Ingwie/OpenAVRc_Dev/documentation/Schema_MegaMini.pdf

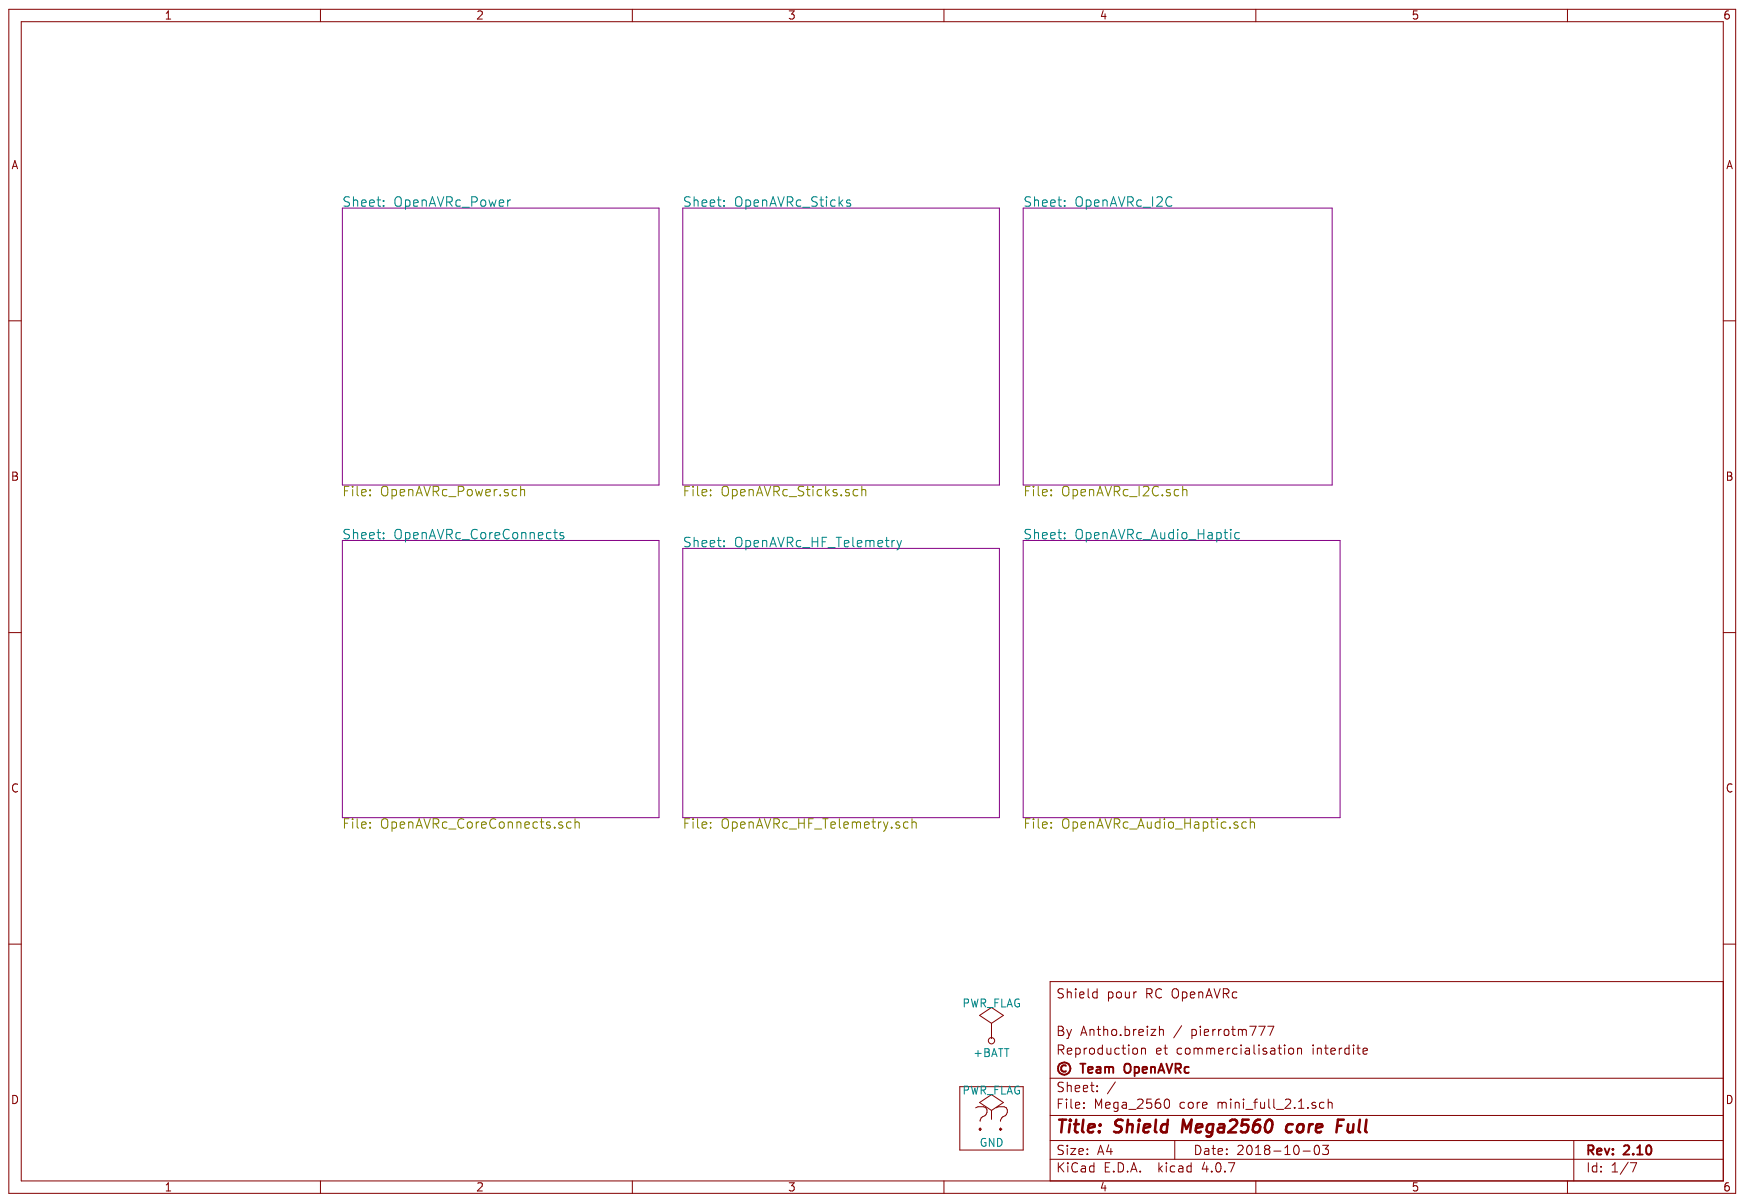
[picture p331: page 1]

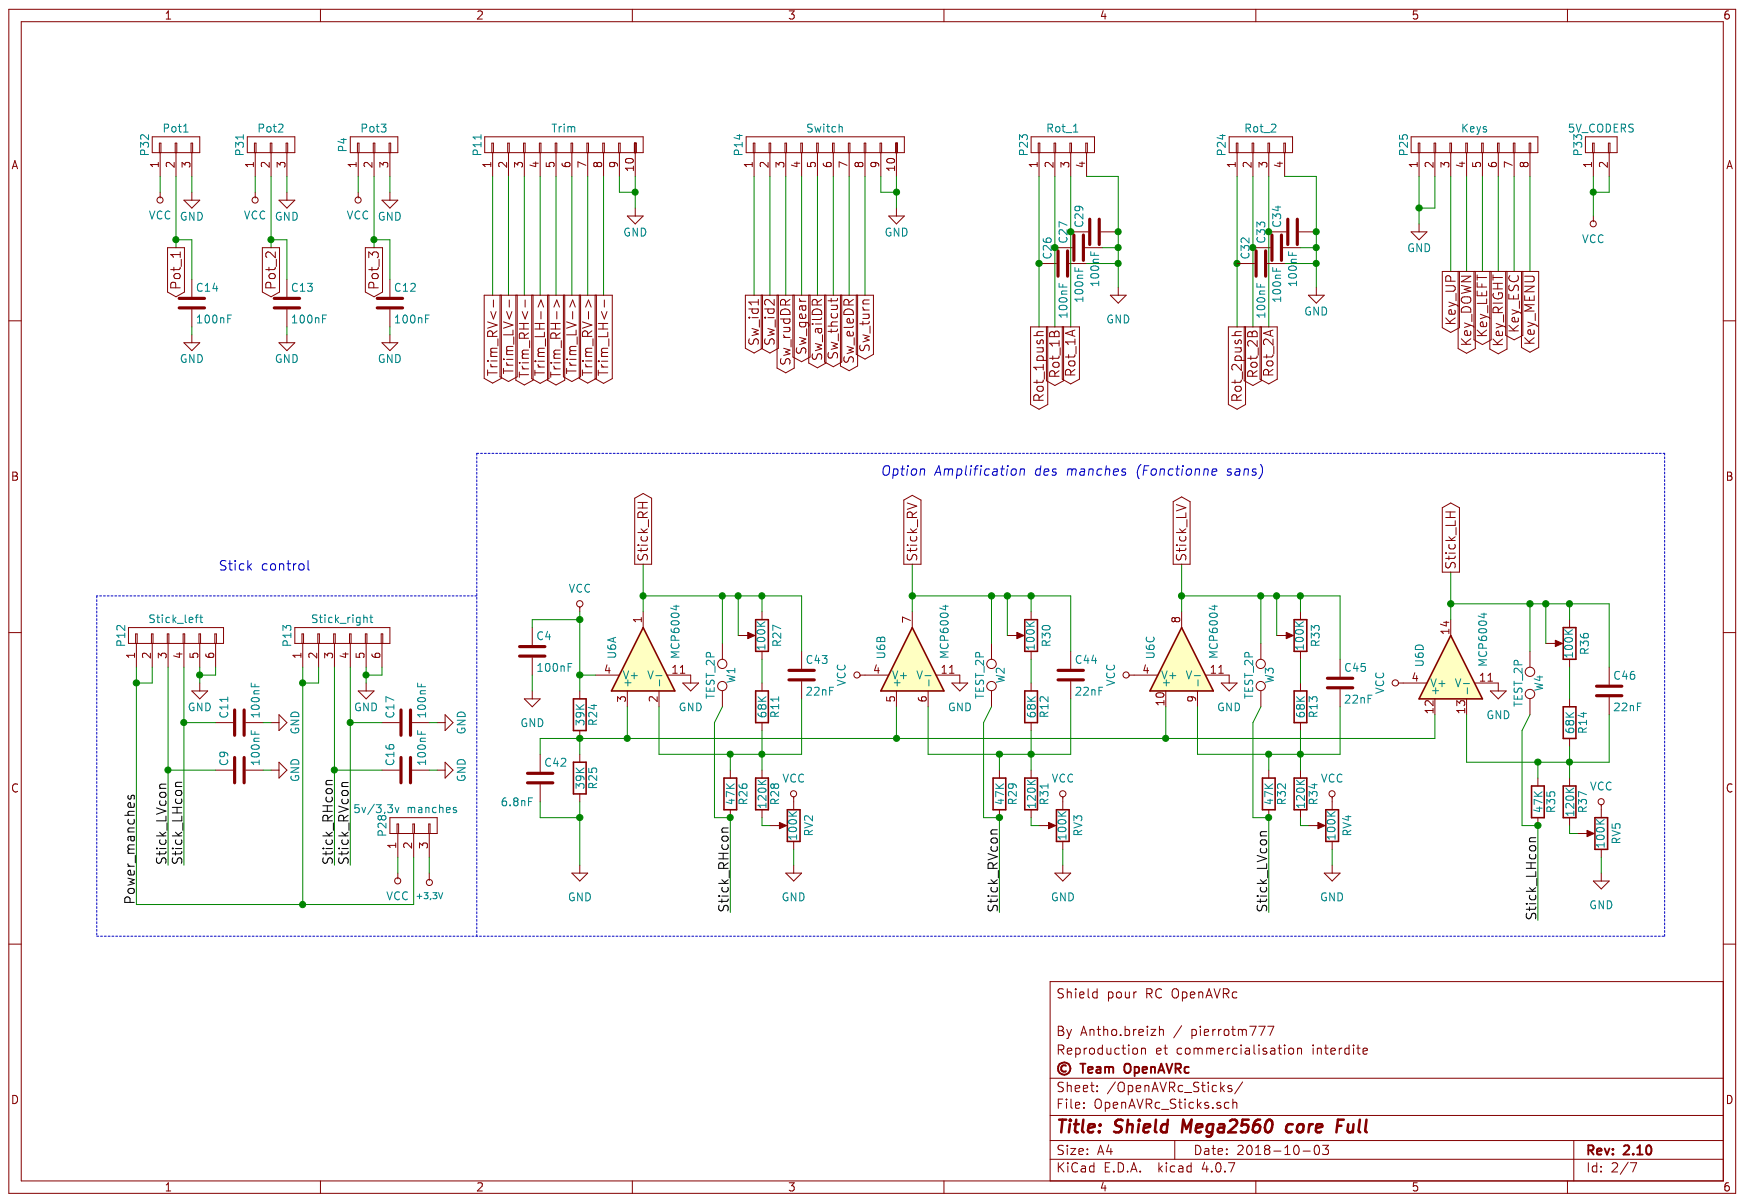
[picture p332: page 2]

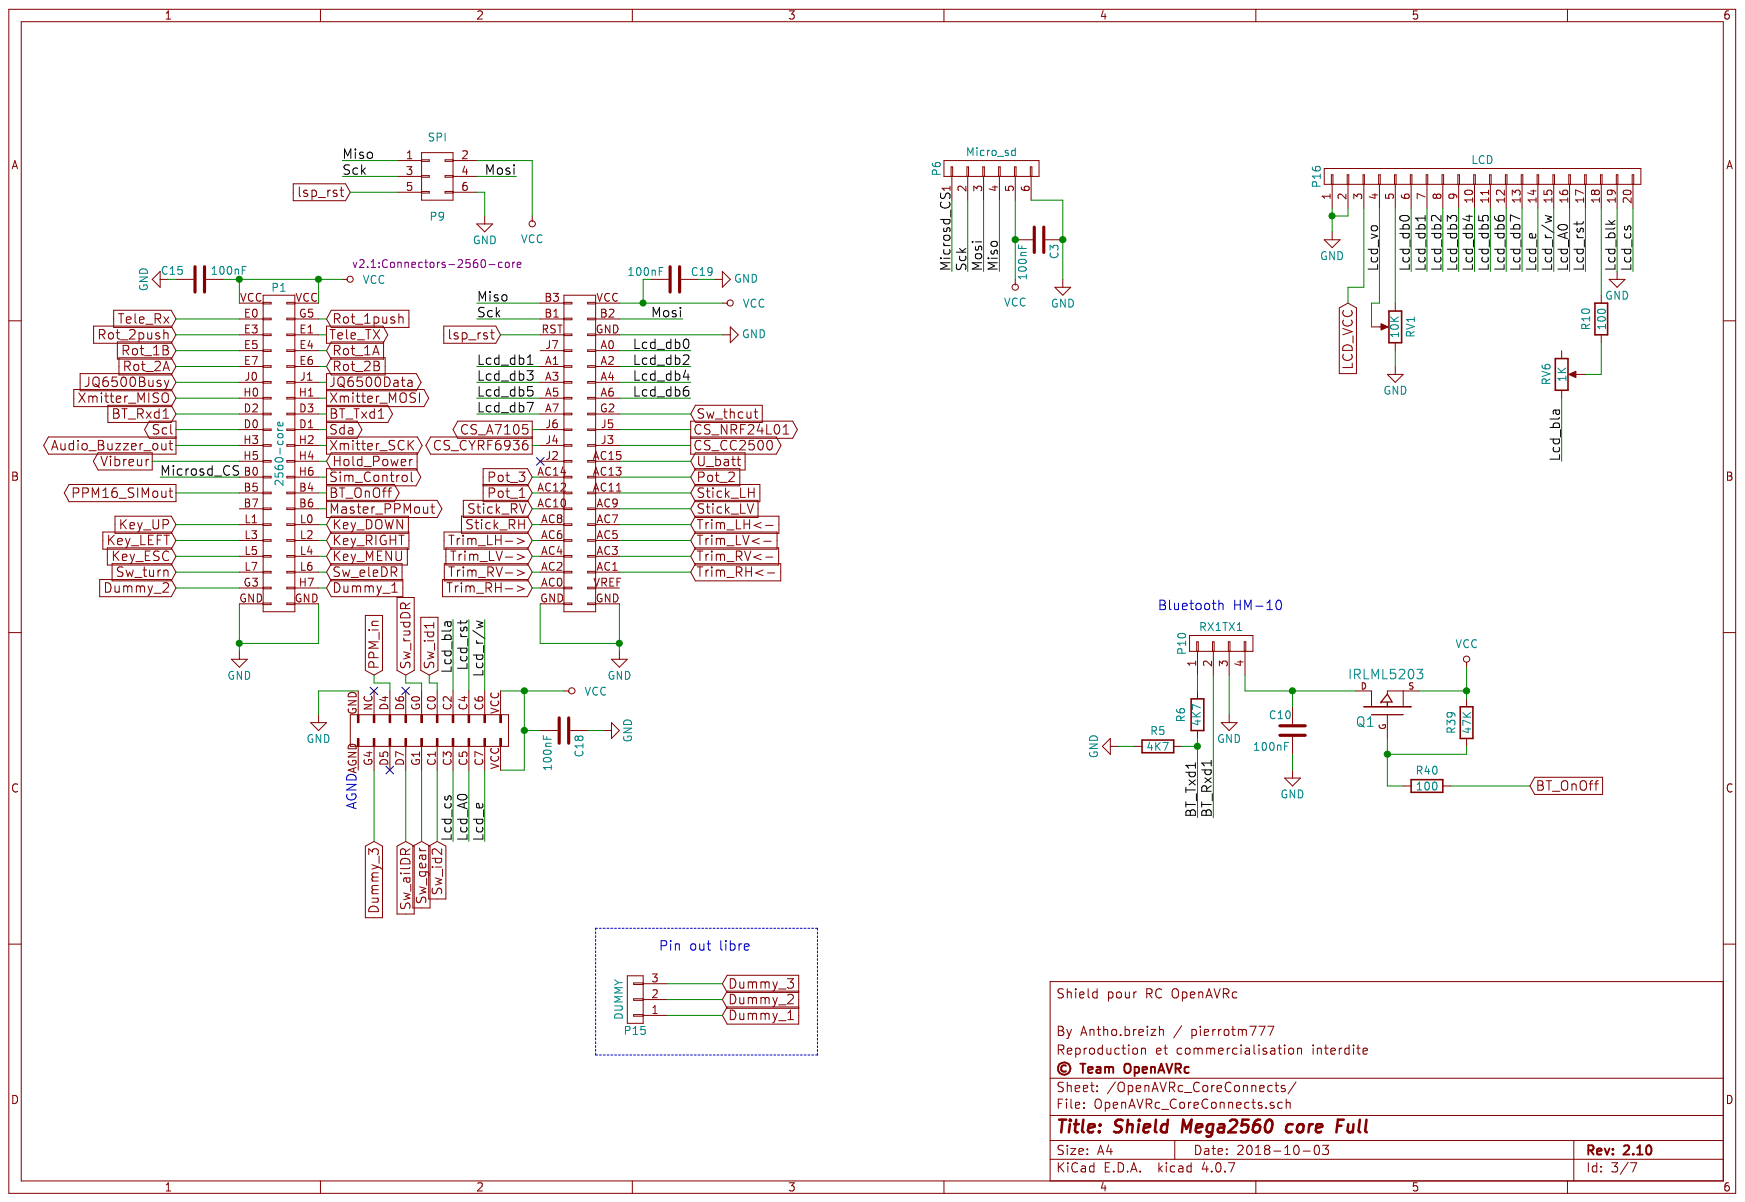
[picture p333: page 3]

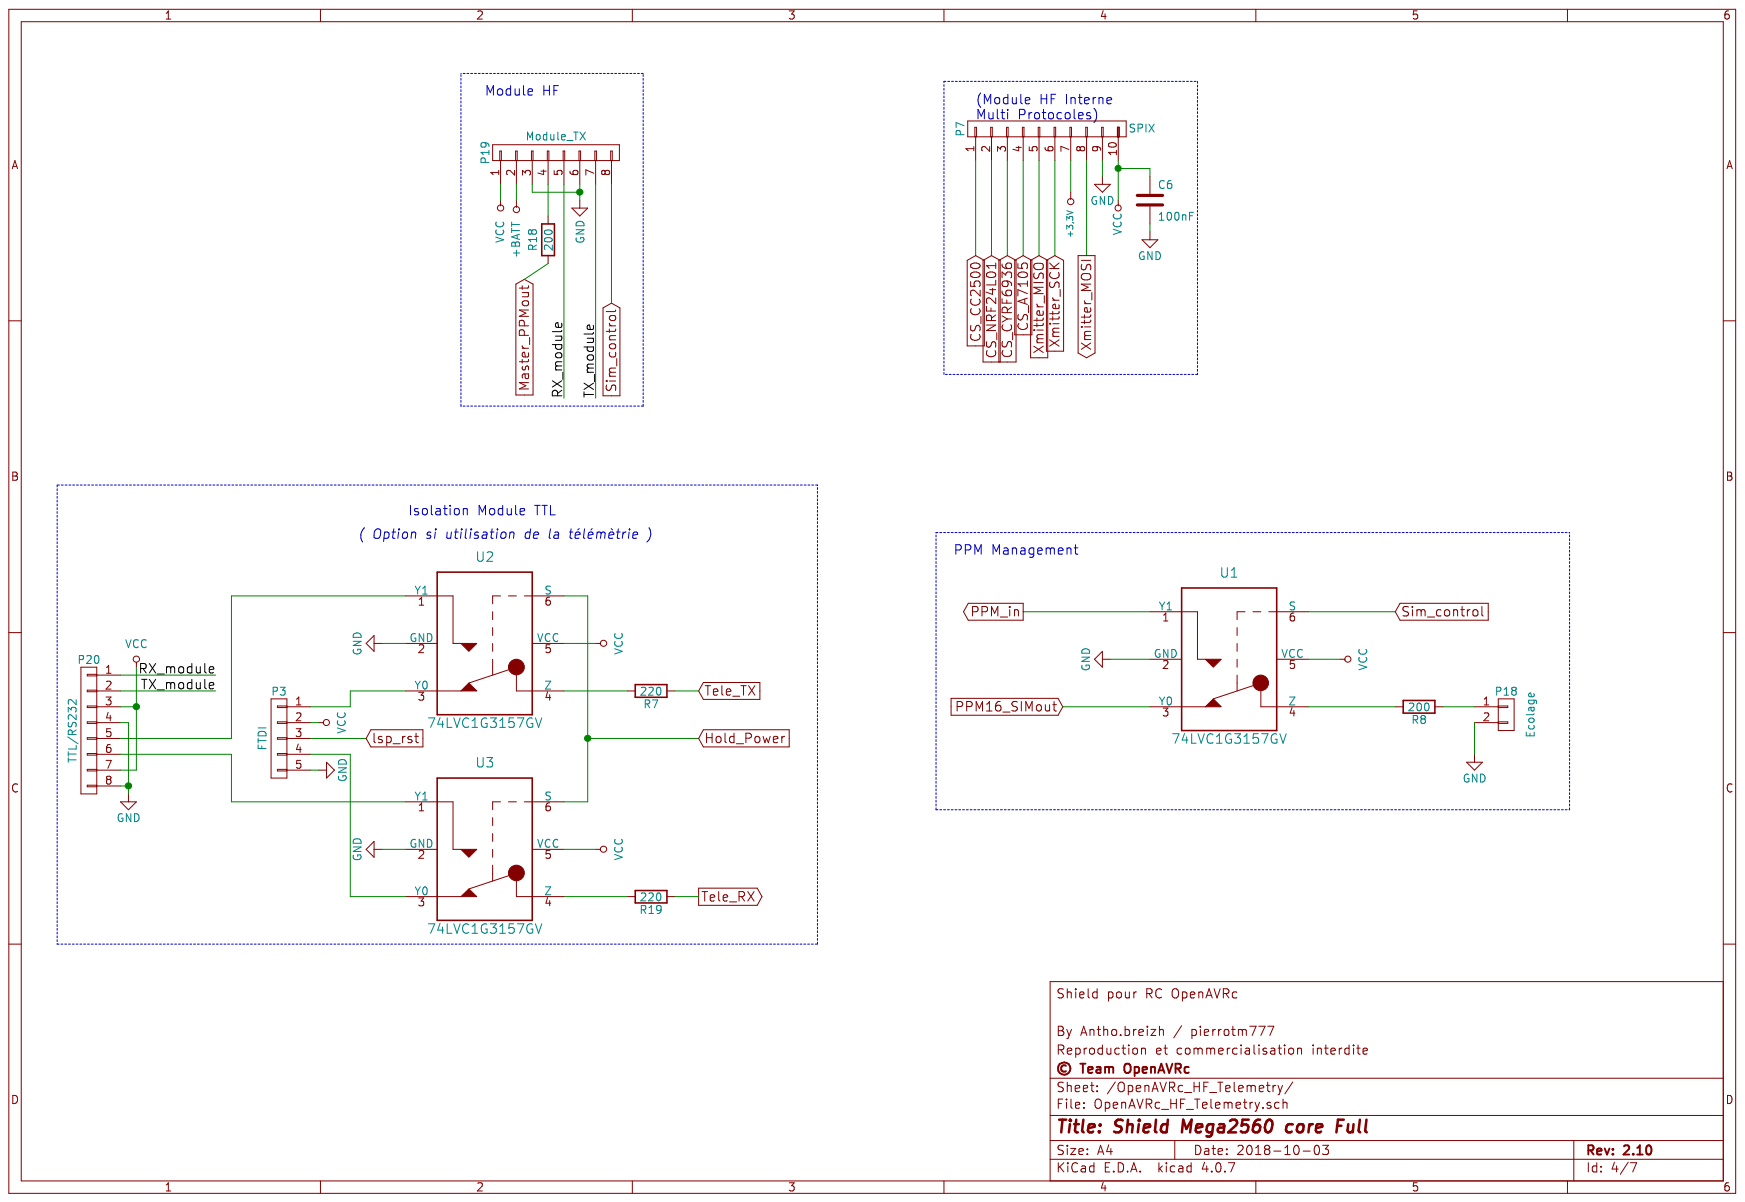
[picture p334: page 4]

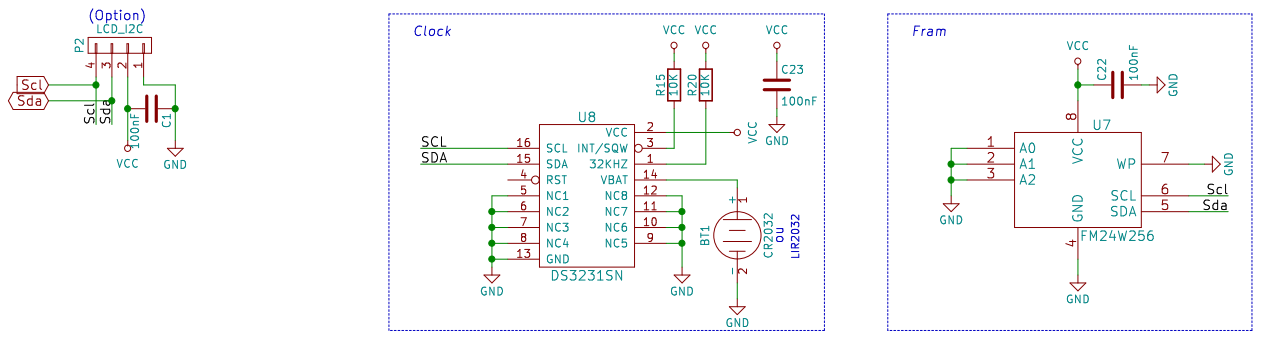
[picture p335: page 5]

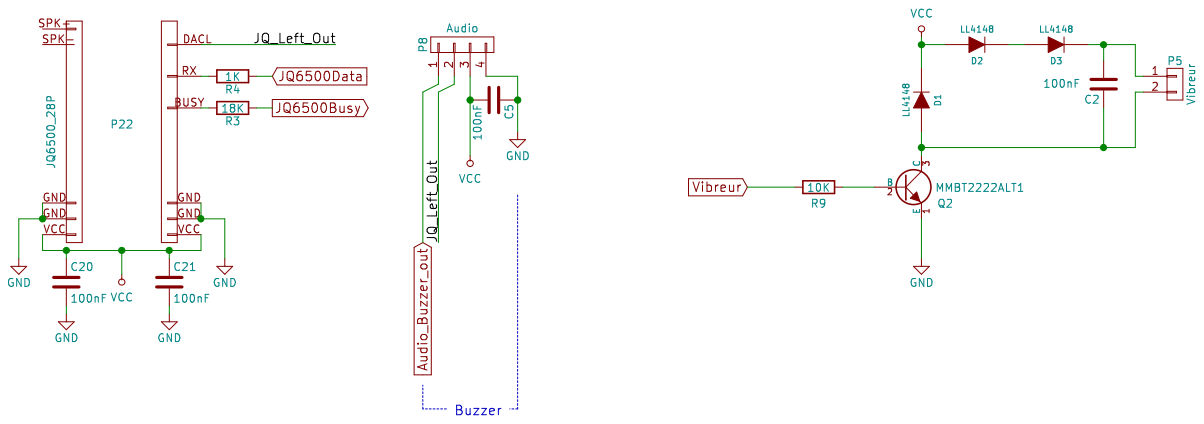
[picture p336: page 6]

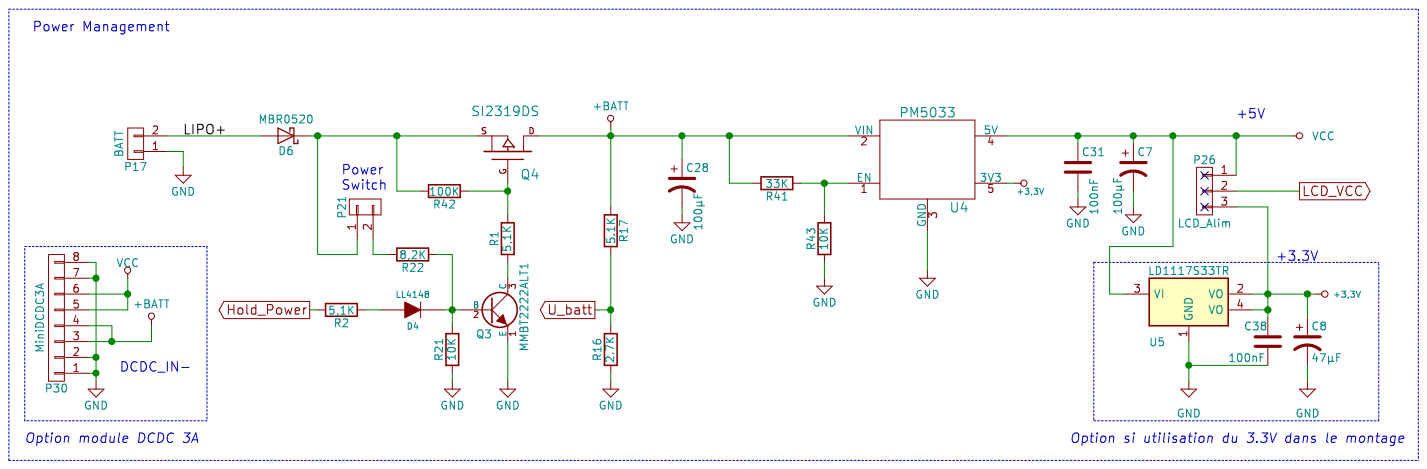
[picture p337: page 7]
