Ingwie/OpenAVRc_Dev/OpenAVRc/targets/evo_v2/xmega_board.h

/*
 * Authors (alphabetical order)
 *
 * - Rick Kilvington (2018).
 *
 */


#ifndef xmega_board_h
#define xmega_board_h

#include "../../OpenAVRc.h"

#define GETADC_COUNT 1  // Used in switches.cpp and keys.cpp.

// USART General defines.
#define USART_SET_BAUD_9K6(usartxn)    _USART_SET_BAUD(usartxn, 12, +4)
#define USART_SET_BAUD_19K2(usartxn)   _USART_SET_BAUD(usartxn, 12, +3 )
#define USART_SET_BAUD_38K4(usartxn)   _USART_SET_BAUD(usartxn, 12, +2)
#define USART_SET_BAUD_57K6(usartxn)   _USART_SET_BAUD(usartxn, 135,-2)
#define USART_SET_BAUD_100K(usartxn)   _USART_SET_BAUD(usartxn, 159,-3)
#define USART_SET_BAUD_115K2(usartxn)  _USART_SET_BAUD(usartxn, 131,-3)
#define USART_SET_BAUD_125K(usartxn)   _USART_SET_BAUD(usartxn, 127,-3)
#define USART_SET_BAUD_230K4(usartxn)  _USART_SET_BAUD(usartxn, 123,-4)

#define _USART_SET_BAUD(usartxn, bsel, bscale) \
  { usartxn.BAUDCTRLA = bsel & 0xFF; usartxn.BAUDCTRLB = ((int8_t) bscale << USART_BSCALE_gp) | (bsel >> 8); }
#define USART_SET_MODE_8N1(usartxn) \
  { usartxn.CTRLC = USART_CMODE_ASYNCHRONOUS_gc | USART_PMODE_DISABLED_gc | (0 << USART_SBMODE_bp) | USART_CHSIZE_8BIT_gc; } // 8N1
#define USART_SET_MODE_8E2(usartxn) \
  { usartxn.CTRLC = USART_CMODE_ASYNCHRONOUS_gc | USART_PMODE_EVEN_gc | (1 << USART_SBMODE_bp) | USART_CHSIZE_8BIT_gc; } // 8E2

#define USART_ENABLE_TX(usartxn) usartxn.CTRLB |= USART_TXEN_bm;

#define USART_PURGE_RX(usartxn) { while (usartxn.STATUS & USART_RXCIF_bm) (void) usartxn.DATA; }

#define USART_ENABLE_RX(usartxn) { \
    usartxn.CTRLB |= USART_RXEN_bm; \
    USART_PURGE_RX(usartxn); \
    usartxn.CTRLA |= USART_RXCINTLVL_MED_gc; \
  } // Enable RX. Flush RX. Enable Interrupt.

#define USART_DISABLE_TX(usartxn) { \
    usartxn.CTRLA &= ~USART_DREINTLVL_gm; \
    usartxn.CTRLB &= ~USART_TXEN_bm; \
  } // Disable Interrupt. Disable TX.

#define USART_DISABLE_RX(usartxn) \
  { usartxn.CTRLA &= ~USART_RXCINTLVL_gm; \
    usartxn.CTRLB &= ~USART_RXEN_bm; \
  } // Disabling RX flushes buffer and clears RXCIF.

#define USART_TRANSMIT_BUFFER(usartxn) { \
    usartxn.CTRLA |= USART_DREINTLVL_MED_gc; \
  } // Enable Data Register Empty Interrupt to transmit buffer.



#define WAIT_USART_BUFFER_EMPTY(usartxn)    while(! (usartxn.STATUS & USART_DREIF_bm) )
#define WAIT_USART_TX_FIN(usartxn)          while(! (usartxn.STATUS & USART_TXCIF_bm) )
#define WAIT_USART_RX_FIN(usartxn)          while(! (usartxn.STATUS & USART_RXCIF_bm) )

#define USART_XCK_PIN_bm    PIN1_bm
#define USART_RXD_PIN_bm    PIN2_bm
#define USART_TXD_PIN_bm    PIN3_bm

// All communication to RF module(s) will use the same pin where possible ... e.g. USART MSPI, USART Asynch and PPM.
// However FrSKy DJT XJT RS232 telemetry may be wired to 2nd serial port.

//#define S1_USART 0
//#define S1_PORT  D
//#define SERIAL1_USART token_paste3(USART, S1_PORT, S1_USART) // e.g. USARTE0
//#define SERIAL1_PORT  token_paste2(PORT, S1_PORT) // e.g. PORTE

#define MULTI_USART SERIAL0_USART
#define DSM_USART   SERIAL0_USART
#define CRSF_USART  SERIAL0_USART
#define SBUS_USART  SERIAL0_USART
#define SUMD_USART  SERIAL0_USART
#define FRSKY_USART SERIAL0_USART

#define MULTI_USART_PORT SERIAL0_PORT
#define DSM_USART_PORT   SERIAL0_PORT
#define CRSF_USART_PORT  SERIAL0_PORT
#define SBUS_USART_PORT  SERIAL0_PORT
#define SUMD_USART_PORT  SERIAL0_PORT
#define FRSKY_USART_PORT SERIAL0_PORT


// token pasting
#define token_paste2_int(x, y) x ## y
#define token_paste2(x, y) token_paste2_int(x, y)
#define token_paste3_int(x, y, z) x ## y ## z
#define token_paste3(x, y, z) token_paste3_int(x, y, z)
#define token_paste4_int(w, x, y, z)  w ## x ## y ## z
#define token_paste4(w, x, y, z) token_paste4_int(w, x, y, z)

// RF Module Timers.
#define RF_PULSES_TC               TCE0 // For PPM and PCM.

#if defined(PWM_BACKLIGHT)
#define PROTO_TC                   TCE1 // For Serial and SPI. PWM backlight available with XMEGA256A3.
#define RF_TIMER_COMPA_VECT        TCE1_CCA_vect
#else
#define PROTO_TC                   TCC0 // For Serial and SPI. NO PWM backlight with XMEGA256C3/D3.
#define RF_TIMER_COMPA_VECT        TCC0_CCA_vect
#endif

#define RF_TIMER                   PROTO_TC.CNT
#define RF_PORT                    PORTE
// Also using VPORT0 as port E for bit bang spi to RF 4in1 module.

#define RF_TIMER_COMPA_REG         PROTO_TC.CCA
#define RF_TIMER_PAUSE_INTERRUPT   PROTO_TC.INTCTRLB &= ~TC0_CCAINTLVL_gm
#define RF_TIMER_RESUME_INTERRUPT  { PROTO_TC.INTCTRLB &= ~TC0_CCAINTLVL_gm; PROTO_TC.INTCTRLB |= TC_CCAINTLVL_HI_gc; } // Level 3 - High Priority.
#define RF_TIMER_CLEAR_COMPA_FLAG  PROTO_TC.INTFLAGS |= TC0_CCAIF_bm // clear ccaif.
#define RF_OUT_PIN                 3
#define RF_OUT_PIN_CTRL_REG        token_paste3(RF_PORT.PIN, RF_OUT_PIN, CTRL) // e.g. "PORTx.PINnCTRL"

#define DEBUG_PIN_HIGH             PORTB.OUTSET = PIN6_bm; // set mpx rf enable pin as high / debug.
#define DEBUG_PIN_LOW              PORTB.OUTCLR = PIN6_bm; // set mpx rf enable pin as low / debug.

void setup_rf_tc(void);
void rf_usart_serial_init(void);


#define CALCULATE_LAT_JIT()  dt = (PROTO_TC.CNT - RF_TIMER_COMPA_REG ) // Calculate latency and jitter.

#if defined(SPIMODULES) // PORTE 0
char rf_usart_mspi_xfer(char c);
uint8_t spi_xfer_4wires_bb(uint8_t c);
void spi_write_3wires_bb(uint8_t c); // Bitbang write.
uint8_t spi_read_3wires_bb(void); // Bitbang read.
//#define RF_SPI_xfer  rf_usart_mspi_xfer
#define RF_SPI_xfer  spi_xfer_4wires_bb
void rf_usart_mspi_init(void);

#define RF_USART                  USARTE0
#define RF_CS_PIN_bm              PIN0_bm

#define RF_CS_CC2500_ACTIVE()     PORTE.OUTCLR = RF_CS_PIN_bm
#define RF_CS_CC2500_INACTIVE()   PORTE.OUTSET = RF_CS_PIN_bm
#define RF_CS_CYRF6936_ACTIVE()   PORTE.OUTCLR = RF_CS_PIN_bm
#define RF_CS_CYRF6936_INACTIVE() PORTE.OUTSET = RF_CS_PIN_bm
#define RF_CS_NRF24L01_ACTIVE()   PORTE.OUTCLR = RF_CS_PIN_bm
#define RF_CS_NRF24L01_INACTIVE() PORTE.OUTSET = RF_CS_PIN_bm
#define RF_CS_A7105_ACTIVE()      PORTE.OUTCLR = RF_CS_PIN_bm
#define RF_CS_A7105_INACTIVE()    PORTE.OUTSET = RF_CS_PIN_bm

// A7105/6 3 Wire SPI patches.
// For a standalone A7105/6 module, SDIO can connect to MISO, MISO to MOSI via a 1K Ohm resistor and hardware SPI can be used.
// For the 4in1 RF Module it is probably simpler to use Bit Banging for all RF chips.
#define SUSPEND_RF_SPI() // { RF_USART.CTRLB = 0; RF_USART.CTRLC = 0; }
#define SET_RF_MOSI_IS_INPUT()   { RF_PORT.DIRCLR = USART_TXD_PIN_bm; }
#define SET_RF_MOSI_IS_OUTPUT()  { RF_PORT.DIRSET = USART_TXD_PIN_bm; }
//#define A7105_Enable_HWSPI()  {}
//#define SPI_READ_3WIRES()  rf_usart_mspi_xfer(0)
//#define SPI_WRITE_3WIRES   rf_usart_mspi_xfer
#define SPI_READ_3WIRES()  spi_read_3wires_bb()
#define SPI_WRITE_3WIRES   spi_write_3wires_bb
#define WAKEUP_RF_SPI()  // { RF_USART.CTRLB = USART_TXEN_bm | USART_RXEN_bm; }

// The following read-modify-write instructions should be compiled to SBI CBI instructions by the compiler.
// e.g. __asm__ ("sbi 0x11,5")
#define RF_MOSI_ON()   __asm__ ("sbi 0x11,3") //{ VPORT0.OUT |= USART_TXD_PIN_bm; }
#define RF_MOSI_OFF()  __asm__ ("cbi 0x11,3") //{ VPORT0.OUT &= ~USART_TXD_PIN_bm; }
#define RF_XCK_ON()    __asm__ ("sbi 0x11,1") //{ VPORT0.OUT |= USART_XCK_PIN_bm; }
#define RF_XCK_OFF()   __asm__ ("cbi 0x11,1") //{ VPORT0.OUT &= ~USART_XCK_PIN_bm; }
#define IS_RF_MOSI_ON  ( VPORT0.IN & USART_TXD_PIN_bm )
#define IS_RF_MISO_ON  ( VPORT0.IN & USART_RXD_PIN_bm )
#endif // SPIMODULES


// Trainer Pulses.
// Xmega uses the same pin for PPM input and output.
#define PULSES_IN_TC         TCF0
#define TRAINER_TC_REG       PULSES_IN_TC.CCA
#define PULSES_IN_TC_VECT    TCF0_CCA_vect
#define TRAINER_TC_VECT      PULSES_IN_TC_VECT
#define TRN_PULSES_IN_PIN    3
#define TRN_PULSES_IN_PORT   PORTF
#define TRN_PULSES_IN_PIN_CTRL_REG   token_paste3(TRN_PULSES_IN_PORT.PIN, TRN_PULSES_IN_PIN, CTRL) // e.g. "PORTF.PIN1CTRL"

#define PULSES_OUT_TC        TCF0
#define TRN_PULSES_OUT_PIN   3
#define TRAINER_PORT         PORTF
#define TRN_PULSES_OUT_PIN_CTRL_REG  token_paste3(TRAINER_PORT.PIN, TRN_PULSES_OUT_PIN, CTRL)
void setup_trainer_tc(void);


// Teacher / Pupil Mode.
#define DISABLE_TRAINER_INTERRUPT()  PULSES_IN_TC.INTCTRLB &= ~TC0_CCAINTLVL_gm
#define ENABLE_TRAINER_INTERRUPT()   { PULSES_IN_TC.INTCTRLB &= ~TC0_CCAINTLVL_gm; PULSES_IN_TC.INTCTRLB |= TC_CCAINTLVL_MED_gc; } // Level 2 - Medium Priority.
#define WAIT_PUPIL()                 ENABLE_TRAINER_INTERRUPT()
#define PPM16_CONF()                 DISABLE_TRAINER_INTERRUPT()


// Switch cross mapping.
#define SW_Jup SW_ID0
#define SW_Jmi SW_ID1
#define SW_Jdn SW_ID2

#define SW_Gdn SW_GEA
#define SW_Ldn SW_RUD
#define SW_Odn SW_ELE

#define SW_N SW_THR
#define SW_I SW_AIL
#define SW_M SW_TRN


// MPX
#define MPX_USART       USARTE0
#define MPX_PORT        PORTE


//#if defined(VOICE_JQ6500)
#define VOICE_USART       USARTC0
#define VOICE_USART_PORT  PORTC
#define VOICE_BUSY_PORT   PORTF
#define VOICE_BUSY_PIN    4
#define VOICE_BUSY_PIN_CTRL_REG   token_paste3(PORTF.PIN, VOICE_BUSY_PIN, CTRL) // e.g. "PORTF.PIN4CTRL"
#define VOICE_BUSY       ((~VOICE_BUSY_PORT.IN) & (1<<VOICE_BUSY_PIN))
#define VOICE_DRE_VECT    USARTC0_DRE_vect
extern void InitVoiceUartTx();
//#endif

// Audio - Piezo Sounder driver.
#define AUDIO_TC             TCD0
#define AUDIO_COMPARE_REG    AUDIO_TC.CCABUF
#if defined(VOICE)
#define speakerOn()   { AUDIO_TC.CTRLB |= TC0_CCAEN_bm; VOICE_BUSY_PORT.OUTCLR = 1<< VOICE_BUSY_PIN; \
  VOICE_BUSY_PORT.DIRSET = 1<< VOICE_BUSY_PIN;}
#define speakerOff()  { AUDIO_TC.CTRLB &= ~TC0_CCAEN_bm; VOICE_BUSY_PORT.DIRCLR = 1<< VOICE_BUSY_PIN;}
#else
#define speakerOn()   { AUDIO_TC.CTRLB |= TC0_CCAEN_bm ;}
#define speakerOff()  { AUDIO_TC.CTRLB &= ~TC0_CCAEN_bm ;}
#endif
#define OD_AUDIO_bm          PIN0_bm


// Trims Button  Matrix.
#define IE_TRIM_COL_A_bm    PIN4_bm
#define IE_TRIM_COL_B_bm    PIN5_bm
#define IE_TRIM_COL_C_bm    PIN6_bm
#define IE_TRIM_COL_D_bm    PIN7_bm
#define OF_TRIM_ROW_A_bm    PIN2_bm


// Trim Buttons.
void read_trim_matrix(void);
#define TRIMS_PRESSED() false

// 64us Counter / 10ms CCA.
#define MS064_TC                   TCC1
#define COUNTER_64uSH              MS064_TC.CNTH
#define COUNTER_64uSL              MS064_TC.CNTL
#define TIMER_10MS_VECT            TCC1_CCA_vect
#define TIMER_10MS_COMPVAL         MS064_TC.CCA
//#define PAUSE_10MS_INTERRUPT       MS064_TC.INTCTRLB &= ~TC1_CCAINTLVL_gm
#define RESUME_10MS_INTERRUPT      { MS064_TC.INTCTRLB &= ~TC1_CCAINTLVL_gm; MS064_TC.INTCTRLB |=  TC_CCAINTLVL_LO_gc; } // Level 1 - Low Priority.
#define MS064_TC_CLEAR_CCAIF_FLAG  MS064_TC.INTFLAGS |= TC1_CCAIF_bm // clear ccaif.

// SD Card driver.
#define sdDone()
#define SD_IS_HC()              (0)
#define SD_GET_SPEED()          (0)
#define SDCARD_SPI              SPIC
#define SDCARD_PORT             PORTC
#define O_SDCARD_CSN_bm         PIN4_bm
#define select_card()           SDCARD_PORT.OUTCLR = O_SDCARD_CSN_bm
#define SDCARD_CS_N_ACTIVE()    SDCARD_PORT.OUTCLR = O_SDCARD_CSN_bm
#define unselect_card()         SDCARD_PORT.OUTSET = O_SDCARD_CSN_bm
#define SDCARD_CS_N_INACTIVE()  SDCARD_PORT.OUTSET = O_SDCARD_CSN_bm
#define SPI_8M()                MSPI_16M(SDCARD_SPI)
#define SPI_250K()              MSPI_250K(SDCARD_SPI)
#define SPI_START_SPEED()       SPI_250K()
#define LEDON() //   {PORTD.OUTTGL = PIN6_bm;}
#define LEDOFF()   {}

// SPI general.
#define MSPI_250K(spix)  { spix.CTRL &= ~(SPI_CLK2X_bm | SPI_PRESCALER_gm); spix.CTRL |= 0b11 << SPI_PRESCALER_gp ;}
#define MSPI_500K(spix)  { spix.CTRL &= ~(SPI_CLK2X_bm | SPI_PRESCALER_gm); spix.CTRL |= 0b10 << SPI_PRESCALER_gp ;}
#define MSPI_1M(spix)    { spix.CTRL &= ~(SPI_CLK2X_bm | SPI_PRESCALER_gm); spix.CTRL |= 0b10 << SPI_PRESCALER_gp | SPI_CLK2X_bm ;}
#define MSPI_2M(spix)    { spix.CTRL &= ~(SPI_CLK2X_bm | SPI_PRESCALER_gm); spix.CTRL |= 0b01 << SPI_PRESCALER_gp ;}
#define MSPI_4M(spix)    { spix.CTRL &= ~(SPI_CLK2X_bm | SPI_PRESCALER_gm); spix.CTRL |= 0b01 << SPI_PRESCALER_gp | SPI_CLK2X_bm ;}
#define MSPI_8M(spix)    { spix.CTRL &= ~(SPI_CLK2X_bm | SPI_PRESCALER_gm) }
#define MSPI_16M(spix)   { spix.CTRL &= ~(SPI_CLK2X_bm | SPI_PRESCALER_gm); spix.CTRL |=  SPI_CLK2X_bm ;}

// Power driver.
#define PWR_HOLD_PORT        PORTB
#define OB_PWR_HOLD_bm       PIN7_bm
//#define PWR_STATUS_PORT      PORTB
//#define IB_PWR_STATUS_bm     PIN7_bm
#define PWR_LED_PORT         PORTC
#define OC_PWR_LED_bm        PIN2_bm

// Power LED / Backlight driver.
#define BACKLIGHT_PORT        PORTC
#define OC_BACKLIGHT_bm       PIN2_bm
#if !defined(PWM_BACKLIGHT)
#define BACKLIGHT_ON()  (BACKLIGHT_PORT.OUTSET = OC_BACKLIGHT_bm)
#define BACKLIGHT_OFF() (BACKLIGHT_PORT.OUTCLR = OC_BACKLIGHT_bm)
#else
#define BACKLIGHT_ON()  (TCC2.LCMPC = ( (uint8_t) g_eeGeneral.blOnBright)  <<4)
#define BACKLIGHT_OFF() (TCC2.LCMPC = ( (uint8_t) g_eeGeneral.blOffBright) <<4)
#endif

#if defined(PWRMANAGE)
#define UNEXPECTED_SHUTDOWN()    ((mcusr & (RST_WDRF_bm)) || g_eeGeneral.unexpectedShutdown)
#else
#define UNEXPECTED_SHUTDOWN()    (mcusr & (RST_WDRF_bm))
#endif

// Rotary encoder pins.
#define ROT_ENC_PORT               PORTF
#define IF_ROT_ENC_LH_CLK_bm       PIN0_bm
#define ROT_ENC_LH_CLK_CTRL_REG    PORTF.PIN0CTRL
#define IF_ROT_ENC_LH_DIR_bm       PIN1_bm
#define IF_ROT_ENC_RH_CLK_bm       PIN6_bm
#define ROT_ENC_RH_CLK_CTRL_REG    PORTF.PIN6CTRL
#define IF_ROT_ENC_RH_DIR_bm       PIN7_bm

#define REA_DOWN()    switchState((EnumKeys)BTN_REa)
#define REB_DOWN()    switchState((EnumKeys)BTN_REb)
#define ROTENC_DOWN() (REA_DOWN() || REB_DOWN())

#define ENABLEROTENCAISR()     {}
#define ENABLEROTENCBISR()     {}
#define DISABLEROTENCAISR()    {}
#define DISABLEROTENCBISR()    {}

// TWI / I2C.
#define FRAM_RTC_TWI              TWIC
#define FRAM_RTC_TWI_TWIM_VECT    TWIC_TWIM_vect

// EEPROM driver.
#define EEPROM_EnableMapping()     NVM.CTRLB |= NVM_EEMAPEN_bm
#define EEPROM_DisableMapping()    NVM.CTRLB &= ~NVM_EEMAPEN_bm
#define NVM_EXEC()                 _PROTECTED_WRITE(NVM.CTRLA, 0b1)
void EEPROM_WaitForNVM(void);
void EEPROM_FlushBuffer(void);

// Bluetooth Pins
#if defined(BLUETOOTH)
#define BT_KEY_ON()
#define BT_KEY_OFF()
#define BT_IS_IN_AT_MODE          (PORTB & OUT_B_BT_KEY) // Not known for HC06.
#define BT_IS_CONNECTED           (!0) // Mega2560 had a bug which always read as connected. Also had a pull up :).
#define BT_POWER_ON()             (PORTB.OUTSET = PIN6_bm)
#define BT_POWER_OFF()            (PORTB.OUTCLR = PIN6_bm)
#define BT_POWER_IS_ON()          (PORTB.IN & PIN6_bm)
#endif

#if !defined(SIMU)
#if defined(EXTERNALEEPROM)
#define ADDRESS_EXTERN_EEPROM  (0x50 << 1) // 0x50 with all strap closed on ZS042 module (or alone), EEPROM FM24W256, see datasheet
#define EEPROMREADBLOCK(a, b, c)   Ext_eeprom_read_block(a, b, c) //External EEPROM
#else
#define EEPROMREADBLOCK(a, b, c) \
  memcpy(a, (const void *) (b + MAPPED_EEPROM_START), c) // Xmega EEPROM is memory mapped for read access.
#endif

#endif // ! SIMU

#endif // xmega_board_h
