Ingwie/OpenAVRc_Dev/OpenAVRc/OpenAVRc.h

/*
**************************************************************************
*                                                                        *
*                 ____                ___ _   _____                      *
*                / __ \___  ___ ___  / _ | | / / _ \____                 *
*               / /_/ / _ \/ -_) _ \/ __ | |/ / , _/ __/                 *
*               \____/ .__/\__/_//_/_/ |_|___/_/|_|\__/                  *
*                   /_/                                                  *
*                                                                        *
*              This file is part of the OpenAVRc project.                *
*                                                                        *
*                         Based on code(s) named :                       *
*             OpenTx - https://github.com/opentx/opentx                  *
*             Deviation - https://www.deviationtx.com/                   *
*                                                                        *
*                Only AVR code here for visibility ;-)                   *
*                                                                        *
*   OpenAVRc is free software: you can redistribute it and/or modify     *
*   it under the terms of the GNU General Public License as published by *
*   the Free Software Foundation, either version 2 of the License, or    *
*   (at your option) any later version.                                  *
*                                                                        *
*   OpenAVRc is distributed in the hope that it will be useful,          *
*   but WITHOUT ANY WARRANTY; without even the implied warranty of       *
*   MERCHANTABILITY or FITNESS FOR A PARTICULAR PURPOSE.  See the        *
*   GNU General Public License for more details.                         *
*                                                                        *
*       License GPLv2: http://www.gnu.org/licenses/gpl-2.0.html          *
*                                                                        *
**************************************************************************
*/


#ifndef OpenAVRc_h
#define OpenAVRc_h

#include <inttypes.h>
#include <string.h>
#include <stddef.h>
#include <stdlib.h>
#include <stdarg.h>
#include <time.h>
#include <stdio.h>

#include "fifo.h"

#if !defined(SIMU)
  #include <avr/pgmspace.h>
  #include <avr/cpufunc.h>
  #include "pgmtypes.h"
  #define ASSERT(x)
  #include "board_avr.h"
  #include <avr/io.h>
  #include <avr/eeprom.h>
  #include <avr/sleep.h>
  #include <avr/interrupt.h>
  #include <util/delay.h>
  #include <util/atomic.h>
  #include <avr/wdt.h>

  #define FORCEINLINE inline __attribute__ ((always_inline))
  #define NOINLINE __attribute__ ((noinline))
  #define TRACE(...)
  #define SIMU_SLEEP(x)
  #define SIMU_PROCESSEVENTS
  #define MYWDT_RESET(x) wdt_reset()
  #define SIMUBEEP1()
  #define SIMUBEEP2()
  #define SIMU_UNLOCK_MACRO_FALSE(x) (x)
  #define SIMU_UNLOCK_MACRO_TRUE(x) (x)
  #define CONVERT_PTR_UINT(x) ((uint32_t)(x))
  #define CONVERT_UINT_PTR(x) ((uint32_t *)(x))
  #define convertSimuPath(x) (x)
// Fiddle to force compiler to use a pointer
  #define FORCE_INDIRECT(ptr) __asm__ __volatile__ ("" : "=e" (ptr) : "0" (ptr))
  #define MKTIME mk_gmtime
  #define ADAPT_PROTOCOL_TO_SIMU()
  #define ADAPT_PROTOCOL_TO_TX()

  #if defined(U_CLI)
    #include "uCli.h"
    #include "Serial1.h"
  #endif

#else //SIMU define

  #include "targets/simu/simu_interface.h"
  #include "targets/megamini/board_megamini.h" //New reference board
  //#include "targets/mega2560/board_mega2560.h"

#endif


/////////////////DEBUG FUNCTION DEFINITION///////////////////

//#define SHOWDURATIONLCD 1  //Show LCD fast refresh duration
#if defined(SHOWDURATIONLCD)
  #define SHOWDURATIONLCD1 SHOWDURATION1
  #define SHOWDURATIONLCD2 SHOWDURATION2
  #define SHOWDURATION 1
#else
  #define SHOWDURATIONLCD1
  #define SHOWDURATIONLCD2
#endif // defined LCD

//#define SHOWDURATION 1  //Show a duration
#if defined(SHOWDURATION)
static uint16_t DurationValue;
#define SHOWDURATION1                                                        \
  uint16_t t0 = getTmr64uS();                                               \

#define SHOWDURATION2                                                        \
  t0 = getTmr64uS() - t0;                                                   \
  if (t0 > DurationValue) DurationValue = t0;                                \

#else
#define SHOWDURATION1
#define SHOWDURATION2
#endif

#define ROTARY_ENCODERS 2

#define CASE_PERSISTENT_TIMERS(x) x,

#if defined(RTCLOCK)
  #define CASE_RTCLOCK(x) x,
#else
  #define CASE_RTCLOCK(x)
#endif

#if defined(BUZZER)
  #define CASE_BUZZER(x) x,
#else
  #define CASE_BUZZER(x)
#endif

#if defined(AUDIO)
  #define CASE_AUDIO(x) x,
#else
  #define CASE_AUDIO(x)
#endif

#if defined(VOICE)
  #define CASE_VOICE(x) x,
#else
  #define CASE_VOICE(x)
#endif

#if defined(PWM_BACKLIGHT)
  #define CASE_PWM_BACKLIGHT(x) x,
#else
  #define CASE_PWM_BACKLIGHT(x)
#endif

#if defined(FRSKY) && defined(GPS)
  #define CASE_GPS(x) x,
#else
  #define CASE_GPS(x)
#endif

#if defined(VARIO)
  #define CASE_VARIO(x) x,
#else
  #define CASE_VARIO(x)
#endif

#if defined(HAPTIC)
  #define CASE_HAPTIC(x) x,
#else
  #define CASE_HAPTIC(x)
#endif

#if defined(SPLASH)
  #define CASE_SPLASH(x) x,
#else
  #define CASE_SPLASH(x)
#endif

#if defined(FRSKY)
  #define CASE_FRSKY(x) x,
#else
  #define CASE_FRSKY(x)
#endif

#if defined(SDCARD)
  #define CASE_SDCARD(x) x,
#else
  #define CASE_SDCARD(x)
  #define logDelay 0
#endif

#if defined(BLUETOOTH)
  #define CASE_BLUETOOTH(x) x,
  #include "bluetooth.h"
#else
  #define CASE_BLUETOOTH(x)
#endif

#if defined(SCC)
  #define CASE_SCC(x) x,
  #include "scc.h"
#else
  #define CASE_SCC(x)
#endif

#if defined(HELI)
  #define CASE_HELI(x) x,
#else
  #define CASE_HELI(x)
#endif

#if defined(TEMPLATES)
  #define CASE_TEMPLATES(x) x,
#else
  #define CASE_TEMPLATES(x)
#endif

#if defined(FLIGHT_MODES)
  #define CASE_FLIGHT_MODES(x) x,
#else
  #define CASE_FLIGHT_MODES(x)
#endif

#if defined(CURVES)
  #define CASE_CURVES(x) x,
#else
  #define CASE_CURVES(x)
#endif

#if defined(GVARS)
  #define CASE_GVARS(x) x,
#else
  #define CASE_GVARS(x)
#endif

#if defined(X_ANY)
  #define CASE_X_ANY(x) x,
#else
  #define CASE_X_ANY(x)
#endif

#if defined(FAI)
  #define IS_FAI_ENABLED() true
  #define IF_FAI_CHOICE(x)
#elif defined(FAI_CHOICE)
  #define IS_FAI_ENABLED() g_eeGeneral.fai
  #define IF_FAI_CHOICE(x) x,
#else
  #define IS_FAI_ENABLED() false
  #define IF_FAI_CHOICE(x)
#endif

#define IS_FAI_FORBIDDEN(idx) (IS_FAI_ENABLED() && idx >= MIXSRC_FIRST_TELEM)

// Build Protocol Mask used by simu to decrypt firmware used protocol
#ifdef SERIAL_PROTOCOL
#define PROTOMASK0 _BV(0)
#else
#define PROTOMASK0 0
#endif
#ifdef PROTO_HAS_CC2500
#define PROTOMASK1 _BV(1)
#else
#define PROTOMASK1 0
#endif
#ifdef PROTO_HAS_CYRF6936
#define PROTOMASK2 _BV(2)
#else
#define PROTOMASK2 0
#endif
#ifdef PROTO_HAS_A7105
#define PROTOMASK3 _BV(3)
#else
#define PROTOMASK3 0
#endif
#ifdef PROTO_HAS_NRF24L01
#define PROTOMASK4 _BV(4)
#else
#define PROTOMASK4 0
#endif
#define PROTOMASK PROTOMASK0|PROTOMASK1|PROTOMASK2|PROTOMASK3|PROTOMASK4//|PROTOMASK5

// RESX range is used for internal calculation; The menu says -100.0 to 100.0; internally it is -1024 to 1024 to allow some optimizations
#define RESX_SHIFT 10
#define RESX       1024
#define RESXu      1024u
#define RESXul     1024ul
#define RESXl      1024l
#define RESX125PC  0x500 // RESX @ 125% (1280)

#include "myeeprom.h"
#include "gui/gui.h"

#define NUM_SWITCHES     7
#define IS_3POS(sw)      ((sw) == 0)
#define IS_MOMENTARY(sw) (sw == SWSRC_TRN)

#define NUM_PSWITCH      (SWSRC_LAST_SWITCH-SWSRC_FIRST_SWITCH+1)

#define KEY_ENTER        KEY_MENU
#define KEY_PLUS         KEY_RIGHT
#define KEY_MINUS        KEY_LEFT


#define memclear(p, s) memset(p, 0, s)

#if defined(PCB_EVO)
  #define IS_POT_AVAILABLE(x)       ( (x)==POT1 || (x)==POT2 )
  #define IS_POT_MULTIPOS(x)        (false)
  #define IS_POT_WITHOUT_DETENT(x)  (false)
#else
  #define IS_POT_AVAILABLE(x)       (true)
  #define IS_POT_MULTIPOS(x)        (false)
  #define IS_POT_WITHOUT_DETENT(x)  (true)
#endif

#define IS_POT(x)                   ((x)>=POT1 && (x)<=POT_LAST)

#define GET_LOWRES_POT_POSITION(i)  (getValue(MIXSRC_FIRST_POT+(i)) >> 4)
#define SAVE_POT_POSITION(i)        g_model.potsWarnPosition[i] = GET_LOWRES_POT_POSITION(i)

#define IF_ROTARY_ENCODERS(x) x,
#define ROTENCDEBOUNCEVAL _BV(2)
  PACK (typedef struct {
    uint8_t A:4;
    uint8_t B:4;
  }) rotEncDebounce_t;
  extern rotEncDebounce_t rotEncDebounce;

#define PPM_CENTER 1500

#if defined(PPM_CENTER_ADJUSTABLE)
  #define PPM_CH_CENTER(ch) (PPM_CENTER+limitAddress(ch)->ppmCenter)
  #define FULL_CHANNEL_OUTPUTS(ch) (channelOutputs[ch] + ((limitAddress(ch)->ppmCenter)>>2))
#else
  #define PPM_CH_CENTER(ch) (PPM_CENTER)
  #define FULL_CHANNEL_OUTPUTS(ch) channelOutputs[ch]
#endif

#include "misclib.h"

#define tmr10ms_t uint16_t

/**
* \file  OpenAVRc.h
* \fn    Macro: GET_10MS_TICK()
* \brief Return the current 10 ms tick counter
*/
#define GET_10MS_TICK()                           getTmr10ms()

/**
* \file   OpenAVRc.h
* \def    ELAPSED_10MS_TICK_SINCE(Start10msTick)
* \brief  Returns the amount of elapsed 10msTick since a starting point expressed in 10msTick
* \param  Start10msTick: starting point expressed in 10msTick
* \return The amount of elapsed 10msTicks since the starting point expressed in 10msTick
*/
#define ELAPSED_10MS_TICK_SINCE(Start10msTick)    ((tmr10ms_t)(getTmr10ms() - (Start10msTick)))

/**
* \file   OpenAVRc.h
* \def    MS_TO_10MS_TICK(Ms)
* \brief  Returns the amount of 10msTick corresponding to a duration expressed in ms
* \param  Ms: a duration expressed in ms
* \return The amount of 10msTicks corresponding to a duration expressed in ms
*/
#define MS_TO_10MS_TICK(Ms)                       ((tmr10ms_t)(((Ms) + 9) / 10))

/**
* \file   OpenAVRc.h
* \def    _10MS_TICK_TO_MS(_10MsTick)
* \brief  Returns the amount of ms corresponsding to a duration expressed in 10msTick
* \param  Ms: a duration expressed in ms
* \return The amount of ms corresponding to a duration expressed in 10msTick
*/
#define _10MS_TICK_TO_MS(_10MsTick)               ((_10MsTick) * 10)

/**
* \file   OpenAVRc.h
* \def    ELAPSED_64uS_TICK_SINCE(Start64uSTick)
* \brief  Returns the amount of elapsed 64uSTick since a starting point expressed in 64uSTick
* \param  Start64uSTick: starting point expressed in 64uSTick
* \return The amount of elapsed 64uSTick since a starting point expressed in 64uSTick
*/
#define ELAPSED_64uS_TICK_SINCE(Start64uSTick)  ((uint16_t)(getTmr64uS() - (Start64uSTick)))

/**
* \file   OpenAVRc.h
* \def    US_TO_64US_TICK(Us)
* \brief  Returns the amount of 64uSTick corresponding to a duration expressed in us
* \param  Ms: a duration expressed in ms
* \return The amount of 64uSTick corresponding to a duration expressed in us
*/
#define US_TO_64US_TICK(Us) ((Us)>>6) /* counter is 16MHz/1024=156251 not real 16Khz tick = 64us */

/**
* \file  misclib.h
* \fn    Macro: YIELD_TO_TASK_FOR_MS(TaskList, StartDurationMsVar, DurationMs)
* \brief Yield CPU to the specified task(s) for the specified time (in ms)
* \param TaskList: list of task(s) (separated with ';')
* \param StartDurationMsVar: uint32_t Variable used to stored ms
* \param DurationMs: Yield duration (in ms)
*/
#define YIELD_TO_TASK_FOR_MS(TaskList, StartDurationMsVar, DurationMs) \
                                                    StartDurationMsVar = GET_10MS_TICK();\
                                                    do{\
                                                      do{\
                                                        MYWDT_RESET();\
                                                        TaskList;\
                                                      }while((GET_10MS_TICK() - StartDurationMsVar) < MS_TO_10MS_TICK(DurationMs));\
                                                    }while(0)

/**
* \file  misclib.h
* \fn    Macro: YIELD_TO_TASK(TaskList)
* \brief yield CPU to the specified task(s) (one shot)
* \param TaskList: list of task(s) (separated with ';')
*/
#define YIELD_TO_TASK(TaskList) \
                                                    do{\
                                                      MYWDT_RESET();\
                                                      TaskList;\
                                                    }while(0)

#define PRIO_TASK_LIST()           checkMixer()


#define T1900_OFFSET 1900
extern time_t g_rtcTime;
extern uint8_t g_ms100; // global to allow time set function to reset to zero
void rtcInit();
void rtcSetTime(struct tm * t);
uint8_t rtcReadTemp(int16_t * temp);

extern volatile tmr10ms_t g_tmr10ms;

extern tmr10ms_t Bind_tmr10ms;

FORCEINLINE uint16_t getTmr10ms();

FORCEINLINE uint16_t getTmr64uS();

void checkMixer();

typedef int8_t rotenc_t;
typedef int16_t getvalue_t;
typedef uint8_t mixsrc_t;
typedef int8_t swsrc_t;


#if defined(NAVIGATION_STICKS)
  extern uint8_t getSticksNavigationEvent();
  extern uint8_t StickScrollAllowed;
  extern uint8_t StickScrollTimer;
  #define STICK_SCROLL_TIMEOUT          9
  #define STICK_SCROLL_DISABLE()        StickScrollAllowed = 0
#else
  #define STICK_SCROLL_DISABLE()
#endif

#if defined(CPUM2560)
#include "Serial0.h"
#include "pulses/pulses_avr.h"
#include "eeprom_common.h"
#include "eeprom_rlc.h"
#endif
#if defined(CPUXMEGA)
#include "targets/evo_v2/xmega_board.h"
#include "Serial0.h"
#include "pulses/pulses_avr.h"
#include "eeprom_common.h"
#include "eeprom_rlc.h"
#endif


#define MASK_CFN_TYPE  uint32_t  // current max = 32 function switches
#define MASK_FUNC_TYPE uint8_t   // current max = 8 functions

typedef struct {
  MASK_FUNC_TYPE activeFunctions;
  MASK_CFN_TYPE  activeSwitches;
  tmr10ms_t lastFunctionTime[NUM_CFN];

  inline uint8_t isFunctionActive(uint8_t func)
  {
    return activeFunctions & ((MASK_FUNC_TYPE)1 << func);
  }

  void reset()
  {
    memclear(this, sizeof(*this));
  }
} CustomFunctionsContext;


//  Dimension of Arrays
#define DIM(a) ((sizeof a) / (sizeof *a))

#if defined(TEMPLATES)
  #include "templates.h"
#endif

extern const pm_uint8_t bchout_ar[];
extern const pm_uint8_t modn12x3[];


//convert from mode 1 to mode stickMode
//NOTICE!  =>  0..3 -> 0..3
#define RUD_STICK 0
#define ELE_STICK 1
#define THR_STICK 2
#define AIL_STICK 3
#define CONVERT_MODE(x)  (((x)<=AIL_STICK) ? pgm_read_byte_near(modn12x3 + 4*systemBolls.stickMode + (x)) : (x) )

extern uint8_t channel_order(uint8_t x);

enum BaseCurves {
  CURVE_NONE,
  CURVE_X_GT0,
  CURVE_X_LT0,
  CURVE_ABS_X,
  CURVE_F_GT0,
  CURVE_F_LT0,
  CURVE_ABS_F,
  CURVE_BASE
};

#define THRCHK_DEADBAND               16

#define SPLASH_NEEDED()               (!g_eeGeneral.splashMode)

#if defined(FSPLASH)
  #define SPLASH_INFINITE_MS          (10*60*1000UL)  // 10 minutes = infinite
  #define SPLASH_DEFAULT_TIMEOUT_MS   (4000)  // 4 seconds
  #define SPLASH_TIMEOUT_MS           (g_eeGeneral.splashMode == 0 ? MS_TO_10MS_TICK(SPLASH_INFINITE_MS) : (MS_TO_10MS_TICK(SPLASH_DEFAULT_TIMEOUT_MS) * (g_eeGeneral.splashMode & 0x03)))
#else
  #define SPLASH_TIMEOUT_MS           (4000)  // 4 seconds
#endif

#define NAVIGATION_RE_IDX()         (g_eeGeneral.reNavigation - 1)
#define IS_RE_NAVIGATION_ENABLE()   g_eeGeneral.reNavigation

#define HEART_TIMER_10MS              1
#define HEART_TIMER_PULSES            2
#define HEART_WDT_CHECK               (HEART_TIMER_10MS + HEART_TIMER_PULSES)

extern uint8_t heartbeat;


#define MAX_ALERT_TIME   60

struct t_inactivity {
  uint16_t counter;
  uint8_t  sum;
};

extern struct t_inactivity inactivity;

#define LEN_STD_CHARS 40

#if defined(TRANSLATIONS_CZ)
  #define ZCHAR_MAX (LEN_STD_CHARS)
#else
  #define ZCHAR_MAX (LEN_STD_CHARS + LEN_SPECIAL_CHARS)
#endif

char hex2zchar(uint8_t hex);
char idx2char(int8_t idx);
void str2zchar(char *dest, const char *src, uint8_t size); // ASCII to FW
uint8_t zchar2str(char *dest, const char *src, uint8_t size); // FW to ASCII

#include "keys.h"

uint8_t switchState(EnumKeys enuk);
uint8_t trimDown(uint8_t idx);

uint16_t evalChkSum();

#if defined(VOICE)
  #define MESSAGE_SOUND_ARG , uint8_t sound
  #define MESSAGE(title, msg, info, sound) message(title, msg, info, sound)
  #define ALERT(title, msg, sound) alert(title, msg, sound)
#else
  #define MESSAGE_SOUND_ARG
  #define MESSAGE(title, msg, info, sound) message(title, msg, info)
  #define ALERT(title, msg, sound) alert(title, msg)
#endif

extern void message(const pm_char *title, const pm_char *s, const char *last MESSAGE_SOUND_ARG);
extern void alert(const pm_char * t, const pm_char * s MESSAGE_SOUND_ARG);

enum PerOutMode {
  e_perout_mode_normal = 0,
  e_perout_mode_inactive_flight_mode = 1,
  e_perout_mode_notrainer = 2,
  e_perout_mode_notrims = 4,
  e_perout_mode_nosticks = 8,
  e_perout_mode_noinput = e_perout_mode_notrainer+e_perout_mode_notrims+e_perout_mode_nosticks
};


extern uint8_t mixerCurrentFlightMode;
extern uint8_t lastFlightMode;
extern uint8_t flightModeTransitionLast;

#define bitfield_channels_t uint16_t

void evalFlightModeMixes(uint8_t mode, uint8_t tick10ms);
void evalMixes(uint8_t tick10ms);
void doMixerCalculations();

void perMain();
NOINLINE void per10ms();

getvalue_t getValue(mixsrc_t i);

uint8_t getSwitch(swsrc_t swtch);
uint8_t getLogicalSwitch(uint8_t idx);

void logicalSwitchesTimerTick();
void logicalSwitchesReset();

extern GETSWITCH_RECURSIVE_TYPE s_last_switch_used;
extern GETSWITCH_RECURSIVE_TYPE s_last_switch_value;
#define LS_RECURSIVE_EVALUATION_RESET() s_last_switch_used = 0

extern swarnstate_t switches_states;
swsrc_t getMovedSwitch();

int8_t getMovedSource();
#define GET_MOVED_SOURCE(min, max) getMovedSource()

#if defined(FLIGHT_MODES)
  extern uint8_t getFlightMode();
#else
  #define getFlightMode() 0
#endif

uint8_t getTrimFlightPhase(uint8_t phase, uint8_t idx);

#if defined(GVARS)
  extern int8_t trimGvar[NUM_STICKS];
  #define TRIM_REUSED(idx) trimGvar[idx] >= 0
#else
  #define TRIM_REUSED(idx) 0
#endif

trim_t getRawTrimValue(uint8_t phase, uint8_t idx);
int16_t getTrimValue(uint8_t phase, uint8_t idx);

void setTrimValue(uint8_t phase, uint8_t idx, int16_t trim);

int16_t getRotaryEncoder(uint8_t idx);
void incRotaryEncoder(uint8_t idx, int8_t inc);

#if defined(GVARS)
  uint8_t getGVarFlightPhase(uint8_t phase, uint8_t idx);
  int16_t getGVarValue(int16_t x, int16_t min, int16_t max, int8_t phase);
  void setGVarValue(uint8_t x, int16_t value, int8_t phase);
  #define GET_GVAR(x, min, max, p) getGVarValue(x, min, max, p)
  #define SET_GVAR(idx, val, p) setGVarValue(idx, val, p)
#else
  #define GET_GVAR(x, ...) (x)
#endif

// highest bit used for small values in mix 128 --> 8 bit is enough
#define GV1_SMALL  128
// highest bit used for large values in mix 256 --> 9 bits is used (8 bits + 1 extra bit from weightMode/offsetMode)
#define GV1_LARGE  256


#define GV_GET_GV1_VALUE(max)        ( (max<=GV_RANGESMALL) ? GV1_SMALL : GV1_LARGE )
#define GV_INDEX_CALCULATION(x,max)  ( (max<=GV1_SMALL) ? (uint8_t) x-GV1_SMALL : ((x&(GV1_LARGE*2-1))-GV1_LARGE) )
#define GV_IS_GV_VALUE(x,min,max)    ( (x>max) || (x<min) )

#define GV_INDEX_CALC_DELTA(x,delta) ((x&(delta*2-1)) - delta)

#define GV_CALC_VALUE_IDX_POS(idx,delta) (-delta+idx)
#define GV_CALC_VALUE_IDX_NEG(idx,delta) (delta+idx)

#define GV_RANGESMALL      (GV1_SMALL - (RESERVE_RANGE_FOR_GVARS+1))
#define GV_RANGESMALL_NEG  (-GV1_SMALL + (RESERVE_RANGE_FOR_GVARS+1))
#define GV_RANGELARGE      (GV1_LARGE - (RESERVE_RANGE_FOR_GVARS+1))
#define GV_RANGELARGE_NEG  (-GV1_LARGE + (RESERVE_RANGE_FOR_GVARS+1))
// for stock we just use as much as possible
#define GV_RANGELARGE_WEIGHT      GV_RANGELARGE
#define GV_RANGELARGE_WEIGHT_NEG  GV_RANGELARGE_NEG
#define GV_RANGELARGE_OFFSET      GV_RANGELARGE
#define GV_RANGELARGE_OFFSET_NEG  GV_RANGELARGE_NEG

extern uint16_t sessionTimer;
extern uint16_t s_timeCumThr;
extern uint16_t s_timeCum16ThrP;

#if defined(OVERRIDE_CHANNEL_FUNCTION)
  typedef int8_t safetych_t;
  #define OVERRIDE_CHANNEL_UNDEFINED -128
  extern safetych_t safetyCh[NUM_CHNOUT];
#endif

extern uint8_t trimsCheckTimer;

void flightReset();

void setGazSource();

PACK(typedef struct {
  uint8_t gazSource:7; // 3-68
  uint8_t enableGaz:1;
}) gazSecurity_t;

extern gazSecurity_t gazSecurity;

#if defined(X_ANY)
#define XANY_SUPPORT    1
#else
#define XANY_SUPPORT    0
#endif

#if defined(SCC)
#define SCC_SUPPORT     1
#else
#define SCC_SUPPORT     0
#endif

#define SYST_BITS_NB (7 + XANY_SUPPORT + SCC_SUPPORT) // Compute the needed system bits at compilation time

// Define the needed integer type which can contain all the system bits
#if (SYST_BITS_NB <= 8)
#define SYST_BITS_UINT_TYPE uint8_t
#else
#define SYST_BITS_UINT_TYPE uint16_t
#endif
#if (SYST_BITS_NB > 16)
Error To mutch systembools !
#endif
PACK(typedef struct {
  SYST_BITS_UINT_TYPE pwrCheck:1;
  SYST_BITS_UINT_TYPE rangeModeIsOn:1;
  SYST_BITS_UINT_TYPE protoMode:1; // Normal, Bind
  SYST_BITS_UINT_TYPE s_mixer_first_run_done:1;
  SYST_BITS_UINT_TYPE puppyPpmSignalOk:1;
#if defined(X_ANY)
  SYST_BITS_UINT_TYPE x_any_Phase:1;
#endif
  SYST_BITS_UINT_TYPE stickMode:2;
#if defined(SCC)
  SYST_BITS_UINT_TYPE scc_sweep_on:1;
#endif
}) systemBolls_t;

extern systemBolls_t systemBolls;

PACK(typedef struct {
  uint8_t unexpectedShutdown:1;
  uint8_t s_write_err:1;  // eprom error reasons (ERR_NONE, ERR_FULL)
  uint8_t s_sync_write:1; // true, false
  uint8_t s_eeDirtyMsk:2; // (EE_NO, EE_GENERAL, EE_MODEL)
  uint8_t unused:3;
}) eepromVars_t;

extern eepromVars_t eepromVars;

extern uint16_t maxMixerDuration;

extern uint16_t g_tmr1Latency_max;
extern uint16_t g_tmr1Latency_min;
extern uint16_t g_guibuild_max;
extern uint16_t g_guibuild_min;
extern uint16_t g_lcddraw_max;
extern uint16_t g_lcddraw_min;
extern uint16_t lastMixerDuration;

#define DURATION_MS_PREC2(x) (((x)*100)>>4)

#if defined(THRTRACE)
  #define MAXTRACE (LCD_W - 8)
  extern uint8_t  s_traceBuf[MAXTRACE];
  extern uint8_t  s_traceWr;
  extern int16_t  s_traceCnt;
  extern uint8_t  s_cnt_10s;
  extern uint16_t s_cnt_samples_thr_10s;
  extern uint16_t s_sum_samples_thr_10s;
  #define RESET_THR_TRACE() s_traceCnt = s_traceWr = s_cnt_10s = s_cnt_samples_thr_10s = s_sum_samples_thr_10s = s_timeCum16ThrP = s_timeCumThr = 0
#else
  #define RESET_THR_TRACE() s_timeCum16ThrP = s_timeCumThr = 0
#endif

uint16_t stackAvailable();
//uint16_t freeRam();

#if defined(SPLASH)
  void doSplash();
#endif

#if MENUS_LOCK == 1
  extern bool readonly;
  extern bool readonlyUnlocked();
  #define READ_ONLY() readonly
  #define READ_ONLY_UNLOCKED() readonlyUnlocked()
#else
  #define READ_ONLY() false
  #define READ_ONLY_UNLOCKED() true
#endif

void checkLowEEPROM();
void checkTHR();
void checkSwitches();
void checkAlarm();
void checkAll();

void getADC();

extern void backlightOn();
extern void backlightFade();
void checkBacklight();


enum Analogs {
#if defined(REV_EVO_V2)
  AREFA, // External reference voltage and negative differential input (Conversions with no gain).
  STICK_RV,
  STICK_RH,
  STICK_LV,
  STICK_LH,
  GAIN_REF_N, // Negative differential input (Conversions with gain).
  POT1, // SLIDER R.
  POT2, // SLIDER L.
  POT_LAST = POT2,
  TX_VOLTAGE,

  ANAL_SWS_1,
  ANAL_SWS_2,
  ANAL_SWS_3,
  ANAL_SWS_4,
  KEYBOARD,
#else
  STICK_RH,
  STICK_LV,
  STICK_RV,
  STICK_LH,
  POT1,
  POT2,
  POT3,
  POT_LAST = POT3,
  TX_VOLTAGE,
#endif
  NUMBER_ANALOG
};

extern uint16_t s_anaFilt[NUMBER_ANALOG];

#undef min // Avoid double declaration in wingw
#undef max
template<class t> FORCEINLINE t min(t a, t b)
{
  return a<b?a:b;
}
template<class t> FORCEINLINE t max(t a, t b)
{
  return a>b?a:b;
}
template<class t> FORCEINLINE t sgn(t a)
{
  return a>0 ? 1 : (a < 0 ? -1 : 0);
}
template<class t> FORCEINLINE t limit(t mi, t x, t ma)
{
  return min(max(mi,x),ma);
}
template<class t> void SWAP(t & a, t & b)
{
  t tmp = b;
  b = a;
  a = tmp;
}

#define IS_IN_RANGE(value,low,high) (!(value<(low)) && (value<((high)+1)))

uint16_t isqrt32(uint32_t n);

void generalDefault();
void modelDefault(uint8_t id);


extern int16_t calc100to256_16Bits(int16_t x); // @@@2 open.20.fsguruh: return x*2.56
extern int16_t calc100to256(int8_t x); // @@@2 open.20.fsguruh: return x*2.56
extern int16_t calc100toRESX_16Bits(int16_t x); // @@@ open.20.fsguruh
extern int16_t calc100toRESX(int8_t x);
extern int16_t calc1000toRESX(int16_t x);
extern int16_t calcRESXto1000(int16_t x);
extern int8_t  calcRESXto100(int16_t x);

extern const char vers_stamp[];

extern uint16_t           g_vbat10mV;
#define GET_TXBATT_BARS() (limit<uint8_t>(2, 20 * ((uint8_t)(g_vbat10mV/10) - g_eeGeneral.vBatMin) / (g_eeGeneral.vBatMax - g_eeGeneral.vBatMin), 20))
#define IS_TXBATT_WARNING() (g_vbat10mV < (g_eeGeneral.vBatWarn*10))


#define g_blinkTmr10ms    (*(uint8_t*)&g_tmr10ms)
extern uint8_t            g_beepCnt;
extern uint8_t            g_beepVal[5];

#include "trainer_input.h"

extern int32_t            chans[NUM_CHNOUT];
extern int16_t            ex_chans[NUM_CHNOUT]; // Outputs (before LIMITS) of the last perMain
extern int16_t            channelOutputs[NUM_CHNOUT];

int16_t intpol(int16_t x, uint8_t idx);
int16_t expo(int16_t x, int16_t k);

#if defined(CURVES)
  int16_t applyCurve(int16_t x, int8_t idx);
#else
  #define applyCurve(x, idx) (x)
#endif

#define applyCustomCurve(x, idx) intpol(x, idx)

#define APPLY_EXPOS_EXTRA_PARAMS_INC
#define APPLY_EXPOS_EXTRA_PARAMS

void applyExpos(int16_t *anas, uint8_t mode APPLY_EXPOS_EXTRA_PARAMS_INC);
int16_t applyLimits(uint8_t channel, int32_t value);

void evalInputs(uint8_t mode);
uint16_t anaIn(uint8_t chan);
extern int16_t calibratedStick[NUM_STICKS+NUM_POTS];

#define FLASH_DURATION 20 /*200ms*/

extern uint8_t beepAgain;
extern uint16_t lightOffCounter;
extern uint8_t flashCounter;
extern uint8_t mixWarning;

FlightModeData *flightModeAddress(uint8_t idx);
ExpoData *expoAddress(uint8_t idx);
MixData *mixAddress(uint8_t idx);
LimitData *limitAddress(uint8_t idx);
int8_t *curveAddress(uint8_t idx);
LogicalSwitchData *lswAddress(uint8_t idx);

// static variables used in evalFlightModeMixes - moved here so they don't interfere with the stack
// It's also easier to initialize them here.
extern int16_t rawAnas[NUM_STICKS];

extern int16_t  anas[NUM_STICKS];
extern int16_t  trims[NUM_STICKS];
extern BeepANACenter bpanaCenter;

extern int8_t s_currCh;
uint8_t getExpoMixCount(uint8_t expo);
void deleteExpoMix(uint8_t expo, uint8_t idx);
void insertExpoMix(uint8_t expo, uint8_t idx);
void applyDefaultTemplate();

void incSubtrim(uint8_t idx, int16_t inc);
void instantTrim();
FORCEINLINE void evalTrims();
void copyTrimsToOffset(uint8_t ch);
void copySticksToOffset(uint8_t ch);
void moveTrimsToOffsets();

#define delayval_t         int8_t

PACK(typedef struct {
  int16_t hold:12;       // 12bits used -RESX to RESX
  uint8_t activeMix:1;
  uint8_t activeExpo:1;
  uint16_t delay:10;     // 10bits used 0 to DELAY_MAX*(100/DELAY_STEP)
  int32_t act:24;
}) MixVal;

extern MixVal mixVal[MAX_MIXERS];

#ifdef BOLD_FONT
inline uint8_t isExpoActive(uint8_t expo)
{
  return mixVal[expo].activeExpo;
}

inline uint8_t isMixActive(uint8_t mix)
{
  return mixVal[mix].activeMix;
}
#else
#define isExpoActive(x) false
#define isMixActive(x) false
#endif

enum CswFunctionFamilies {
  LS_FAMILY_OFS,
  LS_FAMILY_BOOL,
  LS_FAMILY_COMP,
  LS_FAMILY_DIFF,
  LS_FAMILY_TIMER,
  LS_FAMILY_STICKY,
  LS_FAMILY_RANGE,
  LS_FAMILY_EDGE
};

uint8_t lswFamily(uint8_t func);
int16_t lswTimerValue(delayval_t val);

enum FunctionsActive {
  FUNCTION_TRAINER,
  FUNCTION_INSTANT_TRIM = FUNCTION_TRAINER+4,
  FUNCTION_VARIO,
  FUNCTION_BACKLIGHT,
#if defined(SDCARD)
  FUNCTION_LOGS,
#endif
};

#define VARIO_FREQUENCY_ZERO   700/*Hz*/
#define VARIO_FREQUENCY_RANGE  1000/*Hz*/
#define VARIO_REPEAT_ZERO      500/*ms*/
#define VARIO_REPEAT_MAX       80/*ms*/

extern CustomFunctionsContext modelFunctionsContext;

#define isFunctionActive(func) modelFunctionsContext.isFunctionActive(func)
void evalFunctions();
#define customFunctionsReset() modelFunctionsContext.reset()

  // Global rotary encoder registers
extern volatile rotenc_t g_rotenc[ROTARY_ENCODERS];
void ResetToBootloaderWithFlag();

// pointer to telemetry function parser
// serial ones
typedef const void (*p_parseSerialTelemFunction)(uint8_t,uint8_t);
p_parseSerialTelemFunction parseSerialTelemFunction;
extern const void parseSerialTelemFakeByte(uint8_t data, uint8_t error);
extern const void parseSerialTelemFrskyByte(uint8_t data, uint8_t error);
extern const void parseSerialMultiByte(uint8_t data, uint8_t error);
// SPI direct
extern const void parseTelemFrskyByte(uint8_t data);

#if defined (FRSKY)
  // FrSky Telemetry
  #include "telemetry/frsky.h"
  #include "telemetry/ibus.h"
#endif

#define IS_USR_PROTO_FRSKY_HUB()   (g_model.telemetry.usrProto == USR_PROTO_FRSKY)
#define IS_USR_PROTO_WS_HOW_HIGH() (g_model.telemetry.usrProto == USR_PROTO_WS_HOW_HIGH)
#define IS_USR_PROTO_SMART_PORT()  (g_model.telemetry.usrProto == USR_PROTO_SMART_PORT)
#define IS_USR_PROTO_IBUS()        (g_model.telemetry.usrProto == USR_PROTO_IBUS)

#define SET_USR_PROTO_NONE()        (g_model.telemetry.usrProto = USR_PROTO_NONE)
#define SET_USR_PROTO_FRSKY_HUB()   (g_model.telemetry.usrProto = USR_PROTO_FRSKY)
#define SET_USR_PROTO_WS_HOW_HIGH() (g_model.telemetry.usrProto = USR_PROTO_WS_HOW_HIGH)
#define SET_USR_PROTO_SMART_PORT()  (g_model.telemetry.usrProto = USR_PROTO_SMART_PORT)
#define SET_USR_PROTO_IBUS()        (g_model.telemetry.usrProto = USR_PROTO_IBUS)

#define PLAY_REPEAT(x)            (x)                 /* Range 0 to 15 */
#define PLAY_NOW                  0x10
#define PLAY_BACKGROUND           0x20
#define PLAY_INCREMENT(x)         ((uint8_t)(((uint8_t)x) << 6))   /* -1, 0, 1, 2 */

#define AU_MODEL_NAME_NUM_FILE    0xC8 //200 in buildaudiofile models name range 201 to 255
#define AU_PUPPY_GET              0x1A //506
#define AU_PUPPY_LOSS             0x1B //507
#define AU_TELEMETRY_GET          0x1E //510
#define AU_TELEMETRY_LOSS         0x1F //511

/* make sure the defines below always go in numeric order */
enum AUDIO_SOUNDS {
  AU_TADA,
#if defined(VOICE)
  AU_THROTTLE_ALERT,
  AU_SWITCH_ALERT,
  AU_BAD_EEPROM,
  AU_EEPROM_FORMATTING,
#endif
  AU_TX_BATTERY_LOW,
  AU_INACTIVITY,
  AU_ERROR,
  AU_KEYPAD_UP,
  AU_KEYPAD_DOWN,
  AU_MENUS,
  AU_TRIM_MOVE,
  AU_WARNING1,
  AU_WARNING2,
  AU_WARNING3,
  AU_TRIM_MIDDLE,
  AU_POT_MIDDLE,
  AU_MIX_WARNING_1,
  AU_MIX_WARNING_2,
  AU_MIX_WARNING_3,
  AU_TIMER_00,
  AU_TIMER_LT10,
  AU_TIMER_20,
  AU_TIMER_30,

  AU_FRSKY_FIRST,
  AU_FRSKY_BEEP1 = AU_FRSKY_FIRST,
  AU_FRSKY_BEEP2,
  AU_FRSKY_BEEP3,
  AU_FRSKY_WARN1,
  AU_FRSKY_WARN2,
  AU_FRSKY_CHEEP,
  AU_FRSKY_RATATA,
  AU_FRSKY_TICK,
  AU_FRSKY_SIREN,
  AU_FRSKY_RING,
  AU_FRSKY_SCIFI,
  AU_FRSKY_ROBOT,
  AU_FRSKY_CHIRP,
  AU_FRSKY_TADA,
  AU_FRSKY_CRICKET,
  AU_FRSKY_ALARMC,
  AU_FRSKY_LAST,

  AU_NONE=0xff
};

// First message
const pm_char STR_OPENAVRCISLOADING[] PROGMEM = "OpenAVRc is loading ...";
#define  DISPLAY_LOADING_MESSAGE() lcdDrawTextAtt(1*FW, 3*FH, STR_OPENAVRCISLOADING, BOLD)

#if defined(AUDIO)
  #include "audio_avr.h"
#endif

#include "buzzer.h"

#if defined(VOICE)
  #include "targets/mega2560/voice.h"
#endif

#include "translations.h"

#if defined(PERSONAMES)
  #include "personames.h"
#endif

#include "fonts.h"

#if defined(HAPTIC)
  #include "haptic.h"
#endif

#if defined(SDCARD)
  #include "sdcard.h"
#endif

#if defined(X_ANY)
  #include "Xany.h"
  FORCEINLINE void Xany_scheduleTx_AllInstance();
#endif

#if defined(PCM_PROTOCOL)
#include "protocol/PROTO_PCM.h"
#endif

///////////////// PROTOCOLS ///////////////////

enum PROTO_MODE {
  NORMAL_MODE = 0,
  BIND_MODE,
};

enum TxPower {
  TXPOWER_0,
  TXPOWER_1,
  TXPOWER_2,
  TXPOWER_3,
  TXPOWER_4,
  TXPOWER_5,
  TXPOWER_6,
  TXPOWER_7,
};

enum {
  CYRF6936,
  A7105,
  CC2500,
  NRF24L01,
  MULTIMOD,
  TX_MODULE_LAST,
};

enum ProtoCmds {
  PROTOCMD_INIT,
  PROTOCMD_BIND,
  PROTOCMD_RESET,
  PROTOCMD_GETOPTIONS,
};

enum TXRX_State {
  TXRX_OFF,
  TX_EN,
  RX_EN,
};

#define PROTO_NEED_SPI 0x08 // bitmask
#define IS_PROTO_NEED_SPI if (RfOptionSettings.rfProtoNeed & PROTO_NEED_SPI)

#define BOOL1USED 0x01
#define BOOL2USED 0x02
#define BOOL3USED 0x04

PACK(
struct RfOptionSettingsvar_t {
  uint8_t         rfProtoNeed:4;     // See usage in "PROTO_NEED_XX" Def
  uint8_t         rfSubTypeMax:4;       //16 max
  int8_t          rfOptionValue1Min;
  int8_t          rfOptionValue1Max;
  int8_t          rfOptionValue2Min;
  int8_t          rfOptionValue2Max;
  int8_t          rfOptionValue3Max/*:5*/;  //32 max -16 is min
});

PACK(
struct RfOptionSettings_t {
  uint8_t         rfProtoNeed:4;     // See usage in "PROTO_NEED_XX" Def
  uint8_t         rfSubTypeMax:4;       //16 max
  int8_t          rfOptionValue3Max:5;  //32 max -16 is min
  uint8_t         rfOptionBool1Used:1;
  uint8_t         rfOptionBool2Used:1;
  uint8_t         rfOptionBool3Used:1;
  int8_t          rfOptionValue1Min;
  int8_t          rfOptionValue1Max;
  int8_t          rfOptionValue2Min;
  int8_t          rfOptionValue2Max;
  const pm_char*  rfSubTypeNames;
  const pm_char*  rfOptionValue1Name;
  const pm_char*  rfOptionValue2Name;
  const pm_char*  rfOptionValue3Name;
  const pm_char*  rfOptionBool1Name;
  const pm_char*  rfOptionBool2Name;
  const pm_char*  rfOptionBool3Name;
});

void SetRfOptionSettings(uint_farptr_t RfOptSet,
                         const pm_char* rfSubTypeNames,
                         const pm_char* rfOptionValue1Name,
                         const pm_char* rfOptionValue2Name,
                         const pm_char* rfOptionValue3Name,
                         const pm_char* rfOptionBool1Name,
                         const pm_char* rfOptionBool2Name,
                         const pm_char* rfOptionBool3Name);

void LimitRfOptionSettings();

//PPM Defaut

const RfOptionSettingsvar_t RfOpt_PPM_Ser[] PROGMEM = {
  /*rfProtoNeed*/BOOL1USED,
  /*rfSubTypeMax*/6,
  /*rfOptionValue1Min*/-20,
  /*rfOptionValue1Max*/35,
  /*rfOptionValue2Min*/-4,
  /*rfOptionValue2Max*/10,
  /*rfOptionValue3Max*/0,
};

void sendOptionsSettingsPpm();
//PPM

extern struct RfOptionSettings_t RfOptionSettings;
extern void startPulses(enum ProtoCmds Command);
extern uint16_t (*timer_callback)(void);
const void * (*PROTO_Cmds)(enum ProtoCmds);

typedef const void* (*CMDS)(enum ProtoCmds);


/*Load Progmem name for GUI */
#define PROTODEF(proto, module, cmd, name, progmem_name) progmem_name;
#include "protocol/protocol.h"
#undef PROTODEF

#define PROTODEF(proto, module, cmd, name, progmem_name) extern const void * cmd(enum ProtoCmds);
#include "protocol/protocol.h"
#undef PROTODEF

/* Enum protocols */
#define PROTODEF(proto, module, cmd, name, progmem_name) proto,
enum Protocols {
#include "protocol/protocol.h"
  PROTOCOL_COUNT,
};
#undef PROTODEF

/*Load proto, pm_char name and Cmds */
#define PROTODEF(proto, module, cmd, name, progmem_name) { proto, name, cmd },
struct Proto_struct {
  enum Protocols Protocol;
  const pm_char* ProtoName;
  CMDS Cmds; // Cmds
} Protos[] = {
#include "protocol/protocol.h"
};
#undef PROTODEF

/* Load Protocols */
#include "protocol/interface.h"

///////////////// PROTOCOLS ///////////////////


extern void checkBattery();
extern void OpenAVRcClose();
extern void OpenAVRcInit(uint8_t mcusr);

// Re-useable byte array to save having multiple buffers
#define SD_SCREEN_FILE_LENGTH (26)
union ReusableBuffer { // 240 bytes (LogBuffer)

  struct {
    char listnames[LCD_LINES-1][LEN_MODEL_NAME];
    uint16_t eepromfree;

#if defined(SDCARD)
    char menu_bss[POPUP_MENU_MAX_LINES][MENU_LINE_LENGTH];
    char mainname[25]; // used in logs : modelnamex-2013-01-01.log & Voice List read function
#else
    char mainname[LEN_MODEL_NAME];
#endif
  } modelsel; // 164 bytes

#if defined(BLUETOOTH)
  struct {
    uint8_t firstMenuRun;
    uint8_t eeWriteFlag;
    char name_zchar[LEN_BT_NAME];      // FW format
    char name_str[LEN_BT_NAME+1];      // ASCII format
    char pin_zchar[4];                 // FW format
    char pin_str[5];                   // ASCII format
    char peer_name_str[LEN_BT_NAME+1]; // ASCII format
    BtScannSt_t scann;
  } bluetooth; // 94 bytes
#endif
#if defined(SCC)
  SccSt_t Scc;
#endif
#if defined(U_CLI)
  char uCliCmdLine[UCLI_CMD_LINE_MAX_SIZE + 1]; // 101 bytes need to work with bluetooth
#if defined(XMODEM)
  XModemSt_t xx; // 144 bytes
#endif
#endif

  struct {
    int16_t midVals[NUM_STICKS+NUM_POTS];
    int16_t loVals[NUM_STICKS+NUM_POTS];
    int16_t hiVals[NUM_STICKS+NUM_POTS];
    uint8_t state;
  } calib; // 44 bytes

#if defined(SDCARD)
  struct {
    char lines[LCD_LINES-1][SD_SCREEN_FILE_LENGTH+1+1]; // the last char is used to store the flags (directory) of the line
    uint32_t available;
    uint16_t offset;
    uint16_t count;
    char originalName[SD_SCREEN_FILE_LENGTH+1];
  } sdmanager; // 232 bytes

  struct {
    char data[240]; // Sd log buffer
  } logsbuffer; // 240 bytes

#endif
};

extern union ReusableBuffer ReBuff;

void checkFlashOnBeep();

#if defined(FRSKY)
  void convertUnit(getvalue_t & val, uint8_t & unit);
#else
  #define convertUnit(...)
#endif


// Stick tolerance varies between transmitters, Higher is better
#define STICK_TOLERANCE 64

#if defined(FRSKY)
enum BarThresholdIdx {
  THLD_ALT,
  THLD_RPM,
  THLD_FUEL,
  THLD_T1,
  THLD_T2,
  THLD_SPEED,
  THLD_DIST,
  THLD_GPSALT,
  THLD_CELL,
  THLD_CELLS_SUM,
  THLD_VFAS,
  THLD_CURRENT,
  THLD_CONSUMPTION,
  THLD_MAX,
};

typedef uint8_t bar_threshold_t;
#define FILL_THRESHOLD(idx, val) barsThresholds[idx] = 128 + (val)

extern bar_threshold_t barsThresholds[THLD_MAX];
#else
#define FILL_THRESHOLD(idx, val)
#endif

#if defined(FRSKY)
  ls_telemetry_value_t maxTelemValue(source_t channel);
#else
  #define maxTelemValue(channel) 255
#endif


getvalue_t convert8bitsTelemValue(source_t channel, ls_telemetry_value_t value);
getvalue_t convertLswTelemValue(LogicalSwitchData * cs);

#define convertTelemValue(channel, value) convert8bitsTelemValue(channel, value)
#define convertBarTelemValue(channel, value) convert8bitsTelemValue(channel, value)
#define maxBarTelemValue(channel) maxTelemValue(channel)

#if defined(FRSKY)
  lcdint_t applyChannelRatio(source_t channel, lcdint_t val);
  #define ANA_CHANNEL_UNIT(channel) g_model.telemetry.channels[channel].type
#endif

getvalue_t div10_and_round(getvalue_t value);
getvalue_t div100_and_round(getvalue_t value);

#if defined(FRSKY)
uint8_t checkIfModelIsOff();
NOINLINE uint8_t getRssiAlarmValue();

extern const pm_uint8_t bchunit_ar[];

#define FRSKY_MULTIPLIER_MAX 3

enum TelemetryViews {
  TELEMETRY_CUSTOM_SCREEN_1,
  TELEMETRY_CUSTOM_SCREEN_2,
  TELEMETRY_VOLTAGES_SCREEN,
  TELEMETRY_AFTER_FLIGHT_SCREEN,
  TELEMETRY_VIEW_MAX = TELEMETRY_AFTER_FLIGHT_SCREEN
};

extern uint8_t s_frsky_view;

#endif

#define EARTH_RADIUSKM ((uint32_t)6371)
#define EARTH_RADIUS ((uint32_t)111194)

extern void getGpsPilotPosition();
extern void getGpsDistance();
extern void varioWakeup();

#if defined(AUDIO) && defined(BUZZER)
  #define IS_SOUND_OFF() (g_eeGeneral.buzzerMode==e_mode_quiet && g_eeGeneral.beepMode==e_mode_quiet)
#else
  #define IS_SOUND_OFF() (g_eeGeneral.beepMode == e_mode_quiet)
#endif

#if defined(IMPERIAL_UNITS)
  #define IS_IMPERIAL_ENABLE() (1)
#else
  #define IS_IMPERIAL_ENABLE() (0)
#endif

#if defined(FRSKY) && defined(GPS)
  #define IS_GPS_AVAILABLE()         IS_USR_PROTO_FRSKY_HUB() || IS_USR_PROTO_SMART_PORT() || IS_USR_PROTO_IBUS()
#else
  #define IS_GPS_AVAILABLE()         (0)
#endif

#endif //file
