Ingwie/OpenAVRc_Dev/OpenAVRc/translations/en.h

/*
**************************************************************************
*                                                                        *
*                 ____                ___ _   _____                      *
*                / __ \___  ___ ___  / _ | | / / _ \____                 *
*               / /_/ / _ \/ -_) _ \/ __ | |/ / , _/ __/                 *
*               \____/ .__/\__/_//_/_/ |_|___/_/|_|\__/                  *
*                   /_/                                                  *
*                                                                        *
*              This file is part of the OpenAVRc project.                *
*                                                                        *
*                         Based on code(s) named :                       *
*             OpenTx - https://github.com/opentx/opentx                  *
*             Deviation - https://www.deviationtx.com/                   *
*                                                                        *
*                Only AVR code here for visibility ;-)                   *
*                                                                        *
*   OpenAVRc is free software: you can redistribute it and/or modify     *
*   it under the terms of the GNU General Public License as published by *
*   the Free Software Foundation, either version 2 of the License, or    *
*   (at your option) any later version.                                  *
*                                                                        *
*   OpenAVRc is distributed in the hope that it will be useful,          *
*   but WITHOUT ANY WARRANTY; without even the implied warranty of       *
*   MERCHANTABILITY or FITNESS FOR A PARTICULAR PURPOSE.  See the        *
*   GNU General Public License for more details.                         *
*                                                                        *
*       License GPLv2: http://www.gnu.org/licenses/gpl-2.0.html          *
*                                                                        *
**************************************************************************
*/
/* Formatting octal codes available in TR_ strings:
*  \037\x           -sets LCD x-coord (x value in octal)
*  \036             -newline
*  \001 to \034     -extended spacing (value * FW/2)
*  \0               -ends current string
*/

/* NON ZERO TERMINATED STRINGS */
#define LEN_OFFON              "\003"
#define TR_OFFON               "OFF""ON\0"
#define LEN_MMMINV             "\003"
#define TR_MMMINV              "---""INV"
#define LEN_NCHANNELS          "\004"
#define TR_NCHANNELS           "\0014CH\0016CH\0018CH10CH12CH14CH16CH"
#define LEN_VBEEPMODE          "\005"
#define TR_VBEEPMODE           "Quiet""Alarm""NoKey""All\0 "
#define LEN_VRENAVIG           "\003"
#define TR_VRENAVIG            "No REaREb"
#define LEN_VBLMODE            "\004"
#define TR_VBLMODE             "OFF\0""Keys""Ctrl""Both""ON\0 "
#define LEN_TRNMODE            "\003"
#define TR_TRNMODE             "OFF"" +="" :="
#define LEN_TRNCHN             "\003"
#define TR_TRNCHN              "CH1CH2CH3CH4"
#define LEN_VPERSISTENT        "\014"
#define TR_VPERSISTENT         "OFF\0        ""Flight\0     ""Manual Reset"
#define LEN_DSM_PROTOCOLS      "\004"
#define TR_DSM_PROTOCOLS       "LP45""DSM2""DSMX"
#define LEN_VTRIMINC           "\006"
#define TR_VTRIMINC            "Expo\0 ""ExFine""Fine\0 ""Medium""Coarse"
#define LEN_CURVE_TYPES        "\010"
#define TR_CURVE_TYPES         "Standard""Custom\0"
#define LEN_RETA123            "\001"
#define TR_RETA123           "RETA123ab"

#if defined(PWM_BACKLIGHT)
  #define TR_BLONBRIGHTNESS      INDENT "ON Brightn."
  #define TR_BLOFFBRIGHTNESS     INDENT "OFF Brightn."
#endif
#if (SERIAL_PROTOCOL==DSM)
  #define TR_DSM2              "LP45\0 ""DSM2\0 ""DSMX\0 "
#else
  #define TR_DSM2
#endif

#define TR_SPIM               "SPIRfMod"
#define TR_RFPOWER INDENT     "RF Power"

#define TR_PERIOD                INDENT "Period"
#define TR_MODULE              "Module"
#define TR_SUBPROTO            "Sub Proto."
#define TR_RFTUNEFINE         INDENT "Freq.fine"
#define TR_TELEMETRY             "Telemetry"
#define TR_MULTI_VIDFREQ               INDENT "Vid. freq."
#define TR_MULTI_RFPOWER               INDENT "RF Power"
#define TR_MULTI_OPTION                INDENT "Option"
#define TR_AUTOBIND                    INDENT "Autobind"
#define TR_MULTI_DSM_AUTODTECT         INDENT "Autodetect"
#define TR_MULTI_LOWPOWER              INDENT "Low power"
#define TR_MULTI_SERVOFREQ             INDENT "Servo rate"
#define TR_MULTI_FIXEDID               "Fixed ID"
#define TR_MULTI_MAX_THROW             "Max. Throw"
#define TR_MULTI_RFCHAN                "RF Channel"
#define TR_MULTI_OUTPUT                "Output"

#define LEN_VCURVEFUNC         "\003"
#define TR_VCURVEFUNC          "---""x>0""x<0""|x|""f>0""f<0""|f|"
#define LEN_VMLTPX             "\010"
#define TR_VMLTPX              "Add\0    ""Multiply""Replace\0"
#define LEN_VMLTPX2            "\002"
#define TR_VMLTPX2             "+=""*="":="
#define LEN_VMIXTRIMS          "\003"
#define TR_VMIXTRIMS           "OFF""ON\0""Rud""Ele""Thr""Ail"
#define TR_CSWTIMER          "Tim\0 "
#define TR_CSWSTICKY         "Glue\0"
#define TR_CSWRANGE
#define TR_CSWSTAY
#define LEN_VCSWFUNC           "\005"
#define TR_VCSWFUNC            "---\0 " "a=x\0 " "a\173x\0 ""a>x\0 ""a<x\0 " TR_CSWRANGE "|a|>x""|a|<x""AND\0 ""OR\0  ""XOR\0 " TR_CSWSTAY "a=b\0 ""a>b\0 ""a<b\0 ""^}x\0 ""|^|}x" TR_CSWTIMER TR_CSWSTICKY
#define LEN_VFSWFUNC           "\012"
#if defined(VARIO)
  #define TR_VVARIO            "Vario\0    "
#else
  #define TR_VVARIO            "[Vario]\0  "
#endif
#if defined(AUDIO)
  #define TR_SOUND             "Play Sound"
#else
  #define TR_SOUND             "Beep\0     "
#endif
#if defined(HAPTIC)
  #define TR_HAPTIC            "Haptic\0   "
#else
  #define TR_HAPTIC            "[Haptic]\0 "
#endif
#if defined(VOICE)
  #define TR_PLAY_TRACK      "Play Track"
  #define TR_PLAY_BOTH         "Play Both\0"
  #define TR_PLAY_VALUE        "Play Val\0 "
#else
  #define TR_PLAY_TRACK        "[Play Trk]"
  #define TR_PLAY_BOTH         "[Play Bth]"
  #define TR_PLAY_VALUE        "[Play Val]"
#endif
#if defined(SDCARD)
  #define TR_SDCLOGS           "SD Logs\0  "
#else
  #define TR_SDCLOGS           "[SD Logs]\0"
#endif
#if defined(GVARS)
  #define TR_ADJUST_GVAR       "Adjust \0  "
#else
  #define TR_ADJUST_GVAR       "[AdjustGV]"
#endif

#if   defined(OVERRIDE_CHANNEL_FUNCTION)
  #define TR_SF_SAFETY        "Overr.\0   "
#else
  #define TR_SF_SAFETY        "---\0      "
#endif

#define TR_VFSWFUNC          TR_SF_SAFETY "Trainer\0  ""Inst. Trim""Reset\0    " TR_ADJUST_GVAR TR_SOUND TR_PLAY_TRACK TR_PLAY_BOTH TR_PLAY_VALUE TR_VVARIO TR_HAPTIC TR_SDCLOGS "Backlight\0"
#define LEN_VFSWRESET          "\004"
#if defined(FRSKY)
  #define TR_FSW_RESET_TELEM   "Telm"
  #define TR_MODELISON         INDENT "Modele is ON"
#else
  #define TR_FSW_RESET_TELEM
#endif
#define TR_FSW_RESET_TIMERS  "Tmr1""Tmr2"
#define TR_FSW_RESET_ROTENC  "REa\0""REb\0"
#define TR_VFSWRESET           TR_FSW_RESET_TIMERS "All\0" TR_FSW_RESET_TELEM TR_FSW_RESET_ROTENC
#define LEN_FUNCSOUNDS         "\004"
#define TR_FUNCSOUNDS          "Bp1\0""Bp2\0""Bp3\0""Wrn1""Wrn2""Chee""Rata""Tick""Sirn""Ring""SciF""Robt""Chrp""Tada""Crck""Alrm"
#define LEN_VTELEMCHNS         "\004"
#define TR_TELEM_RESERVE
#define TR_TELEM_TIME
#define TR_SWR
#define TR_RX_BATT
#define TR_A3_A4
#define TR_A3_A4_MIN
#define TR_ASPD_MAX            "ASp+"
#define TR_TELEM_RSSI_RX     "Rx\0 "
#define TR_TELEM_TIMERS      "Tmr1""Tmr2"
#define TR_VTELEMCHNS        "---\0""Batt" TR_TELEM_TIME TR_TELEM_RESERVE TR_TELEM_RESERVE TR_TELEM_RESERVE TR_TELEM_RESERVE TR_TELEM_RESERVE TR_TELEM_TIMERS TR_SWR "Tx\0 " TR_TELEM_RSSI_RX TR_RX_BATT "A1\0 ""A2\0 " TR_A3_A4 "Alt\0""Rpm\0""Fuel""T1\0 ""T2\0 ""Spd\0""Dist""GAlt""Cell""Cels""Vfas""Curr""Cnsp""Powr""AccX""AccY""AccZ""Hdg\0""VSpd""ASpd""dTE\0" TR_TELEM_RESERVE TR_TELEM_RESERVE TR_TELEM_RESERVE TR_TELEM_RESERVE TR_TELEM_RESERVE "A1-\0""A2-\0" TR_A3_A4_MIN "Alt-""Alt+""Rpm+""T1+\0""T2+\0""Spd+""Dst+" TR_ASPD_MAX "Cel-""Cls-""Vfs-""Cur+""Pwr+" TR_TELEM_RESERVE TR_TELEM_RESERVE TR_TELEM_RESERVE TR_TELEM_RESERVE TR_TELEM_RESERVE "Acc\0""Time"
#define LENGTH_UNIT_IMP        "ft\0"
#define SPEED_UNIT_IMP         "mph"
#define LENGTH_UNIT_METR       "m\0 "
#define SPEED_UNIT_METR        "kmh"
#if defined(IMPERIAL_UNITS)
  #define LENGTH_UNIT        LENGTH_UNIT_IMP
  #define SPEED_UNIT         SPEED_UNIT_IMP
#else
  #define LENGTH_UNIT        LENGTH_UNIT_METR
  #define SPEED_UNIT         SPEED_UNIT_METR
#endif
#define LEN_VTELEMUNIT       "\003"
#define TR_VTELEMUNIT        "V\0 ""A\0 ""m/s""-\0 " SPEED_UNIT LENGTH_UNIT "@\0 ""%\0 ""mA\0""mAh""W\0 "
#define STR_V                  (STR_VTELEMUNIT+1)
#define STR_A                  (STR_VTELEMUNIT+4)
#define LEN_VTELPROTO          "\007"
#define TR_VTELPROTO           "None\0  ""Hub\0   ""WSHHigh""S.Port\0""iBus\0  "
#define LEN_AMPSRC           "\003"
#define TR_AMPSRC            "---""A1\0""A2\0""FAS""Cel"
#define LEN_VARIOSRC           "\004"
#if defined(FRSKY_SPORT)
  #define TR_VARIOSRC          "VSpd""A1\0 ""A2\0 ""dTE\0"
#else
  #define TR_VARIOSRC          "Alt\0""Alt+""VSpd""A1\0 ""A2\0"
#endif
#define LEN_VTELEMSCREENTYPE "\004"
#define TR_VTELEMSCREENTYPE  "Nums""Bars"
#define LEN_GPSFORMAT          "\004"
#define TR_GPSFORMAT           "DMS\0""NMEA"
#define LEN2_VTEMPLATES        13
#define LEN_VTEMPLATES         "\015"
#define TR_VTEMPLATES          "Clear Mixes\0\0""Simple 4-CH \0""Sticky-T-Cut\0""V-Tail      \0""Elevon\\Delta\0""eCCPM       \0""Heli Setup  \0""Servo Test  \0"
#define LEN_VSWASHTYPE         "\004"
#define TR_VSWASHTYPE          "---\0""120\0""120X""140\0""90\0"
#define LEN_VKEYS              "\005"
#define TR_VKEYS               "Menu\0""Exit\0""Down\0""Up\0  ""Right""Left\0"
#define LEN_VRENCODERS         "\003"
#define TR_VRENCODERS          "REa""REb"
#define TR_STICKS_VSRCRAW      "Rud\0""Ele\0""Thr\0""Ail\0"
#define TR_TRIMS_VSRCRAW       "TrmR""TrmE""TrmT""TrmA"
#define TR_POTS_VSRCRAW      "P1\0 ""P2\0 ""P3\0 "
#define TR_SW_VSRCRAW        "3POS"
#define TR_9X_3POS_SWITCHES  "ID0""ID1""ID2"
#define TR_LOGICALSW         "L1\0""L2\0""L3\0""L4\0""L5\0""L6\0""L7\0""L8\0""L9\0""L10""L11""L12""L13""L14""L15""L16""L17""L18""L19""L20"
#define TR_TRIMS_SWITCHES      "tRl""tRr""tEd""tEu""tTd""tTu""tAl""tAr"
#define TR_ROTARY_ENCODERS   "REa\0""REb\0"
#define TR_ROTENC_SWITCHES   "REA""REB""REN"
#define TR_PHYS_SWITCHES     "THR""RUD""ELE""AIL""GEA""TRN"
#define TR_ON_ONE_SWITCHES     "ON\0""One"
#define TR_EXTRA_3POS_SWITCHES  "XD0""XD1""XD2"
#define LEN_VSRCRAW            "\004"
#define LEN_VSWITCHES          "\003"
#define TR_VSWITCHES         "---" TR_9X_3POS_SWITCHES TR_PHYS_SWITCHES TR_TRIMS_SWITCHES TR_ROTENC_SWITCHES TR_EXTRA_3POS_SWITCHES TR_LOGICALSW TR_ON_ONE_SWITCHES
#if defined(HELI)
  #define TR_CYC_VSRCRAW       "CYC1""CYC2""CYC3"
#else
  #define TR_CYC_VSRCRAW       "[C1]""[C2]""[C3]"
#endif
#define TR_EXTRA_VSRCRAW
#define TR_VSRCRAW             "---\0" TR_STICKS_VSRCRAW TR_POTS_VSRCRAW TR_ROTARY_ENCODERS "MAX\0" TR_CYC_VSRCRAW TR_TRIMS_VSRCRAW TR_SW_VSRCRAW TR_EXTRA_VSRCRAW
#define LEN_VTMRMODES          "\003"
#define TR_VTMRMODES           "OFF""ON\0""THs""TH%""THt"

/* ZERO TERMINATED STRINGS */
#define INDENT               "\001"
#define LEN_INDENT           1
#define INDENT_WIDTH         (FW/2)
#define BREAKSPACE           " "
#define TR_ENTER             "[MENU]"
#define TR_EXIT                "[EXIT]"
#define TR_POPUPS            TR_ENTER "\010" TR_EXIT
#define OFS_EXIT             sizeof(TR_ENTER)
#define TR_MENUWHENDONE        CENTER "\006" TR_ENTER " WHEN DONE"
#define TR_FREE                "free"
#define TR_DELETEMODEL         "DELETE" BREAKSPACE "MODEL"
#define TR_COPYINGMODEL        "Copying model..."
#define TR_MOVINGMODEL         "Moving model..."
#define TR_LOADINGMODEL        "Loading model..."
#define TR_NAME                "Name"
#define TR_TIMER               "Timer"
#define TR_ELIMITS             "E.Limits"
#define TR_ETRIMS              "E.Trims"
#define TR_TRIMINC             "Trim Step"
#define TR_TTRACE              "T-Source"
#define TR_TSWITCH             "T-Switch"
#define TR_TTRIM               "T-Trim"
#define TR_BEEPCTR             "Ctr Beep"
#define TR_PROTO               INDENT "Protocol"
#define TR_PPMFRAME          "PPM frame"
#define TR_MS                  "ms"
#define TR_SWITCH              "Switch"
#define TR_TRIMS               "Trims"
#define TR_FADEIN              "Fade In"
#define TR_FADEOUT             "Fade Out"
#define TR_DEFAULT             "(default)"
#define TR_CHECKTRIMS          CENTER "\006Check\012Trims"
#define OFS_CHECKTRIMS         CENTER_OFS+(9*FW)
#define TR_SWASHTYPE           "Swash Type"
#define TR_COLLECTIVE          "Collective"
#define TR_SWASHRING           "Swash Ring"
#define TR_ELEDIRECTION        "ELE Direction"
#define TR_AILDIRECTION        "AIL Direction"
#define TR_COLDIRECTION        "PIT Direction"
#define TR_MODE                INDENT "Mode"
#define TR_NOFREEEXPO          "No free expo!"
#define TR_NOFREEMIXER         "No free mixer!"
#define TR_INSERTMIX           "INSERT MIX "
#define TR_EDITMIX             "EDIT MIX "
#define TR_SOURCE              INDENT "Source"
#define TR_WEIGHT              "Weight"
#define TR_EXPO                "Expo"
#define TR_SIDE                "Side"
#define TR_DIFFERENTIAL        "Differ"
#define TR_OFFSET              INDENT "Offset"
#define TR_TRIM                "Trim"
#define TR_DREX                "DRex"
#define DREX_CHBOX_OFFSET      30
#define TR_CURVE               "Curve"
#define TR_FLMODE              "Mode"
#define TR_MIXWARNING          "Warning"
#define TR_OFF                 "OFF"
#define TR_MULTPX              "Multpx"
#define TR_DELAYDOWN           "Delay Dn"
#define TR_DELAYUP             "Delay Up"
#define TR_SLOWDOWN            "Slow  Dn"
#define TR_SLOWUP              "Slow  Up"
#define TR_MIXER               "MIXER"
#define TR_CV                  "CV"
#define TR_GV                  "GV"
#define TR_ACHANNEL            "A\004channel"
#define TR_RANGE               INDENT "Range"
#define TR_ALARM               INDENT "Alarm"
#define TR_USRDATA             "UsrData"
#define TR_BLADES              INDENT "Blades"
#define TR_SCREEN              "Screen\001"
#define TR_SOUND_LABEL         "Sound"
#define TR_LENGTH              INDENT "Length"
#define TR_BEEP_LENGTH         INDENT "Beep Length"
#define TR_SPKRPITCH           INDENT "Beep Pitch"
#define TR_HAPTIC_LABEL        "Haptic"
#define TR_HAPTICSTRENGTH      INDENT "Strength"
#define TR_CONTRAST            "Contrast"
#define TR_ALARMS_LABEL        "Alarms"
#define TR_BATTERY_RANGE       "Battery range"
#define TR_BATTERYWARNING      INDENT "Battery Low"
#define TR_INACTIVITYALARM     INDENT "Inactivity"
#define TR_MEMORYWARNING       INDENT "Memory Low"
#define TR_ALARMWARNING        INDENT "Sound Off"
#define TR_RENAVIG             "RotEnc Navig"
#define TR_MINUTEBEEP          INDENT "Minute"
#define TR_BEEPCOUNTDOWN       INDENT "Countdown"
#define TR_PERSISTENT          INDENT "Persist."
#define TR_BACKLIGHT_LABEL     "Backlight"
#define TR_BLDELAY             INDENT "Duration"
#define TR_SPLASHSCREEN        "Splash screen"
#define TR_THROTTLEWARNING     "T-Warning"
#define TR_SWITCHWARNING       "S-Warning"
#define TR_TIMEZONE            "Time Zone"
#define TR_ADJUST_RTC          "Adjust RTC"
#define TR_GPS                 "GPS"
#define TR_RXCHANNELORD        "Rx Channel Ord"
#define TR_STICKS              "Sticks"
#define TR_POTS                "Pots"
#define TR_SLAVE               CENTER "Slave"
#define TR_MODESRC             "Mode\006% Source"
#define TR_MULTIPLIER          "Multiplier"
#define TR_CAL                 "Cal"
#define TR_VTRIM               "Trim- +"
#define TR_MENUTOSTART       CENTER "\010" TR_ENTER " TO START"
#define TR_SETMIDPOINT       CENTER "\004SET STICKS MIDPOINT"
#define TR_MOVESTICKSPOTS    CENTER "\006MOVE STICKS/POTS"
#define TR_RXBATT              "Rx Batt:"
#define TR_TXnRX               "Tx:\0Rx:"
#define OFS_RX                 4
#define TR_ACCEL               "Acc:"
#define TR_NODATA              CENTER "NO DATA"
#define TR_TOTTM1TM2THRTHP     "\037\146SES\036TM1\037\146TM2\036THR\037\146TH%"
#define TR_US                  "us"
#define TR_MENUTORESET         CENTER TR_ENTER " to reset"
#define TR_PPM_TRAINER         "TR"
#define TR_CH                  "CH"
#define TR_MODEL               "MODEL"
#define TR_FP                  "FM"
#define TR_MIX                 "MIX"
#define TR_EEPROMLOWMEM        "EEPROM low mem"
#define TR_ALERT               "\016ALERT"
#define TR_PRESSANYKEYTOSKIP   "Press any key to skip"
#define TR_THROTTLENOTIDLE     "Throttle not idle"
#define TR_ALARMSDISABLED      "Alarms Disabled"
#define TR_PRESSANYKEY         "\010Press any Key"
#define TR_BADEEPROMDATA       "Bad EEprom Data"
#define TR_EEPROMFORMATTING    "Formatting EEPROM"
#define TR_EEPROMOVERFLOW      "EEPROM overflow"
#define TR_MENURADIOSETUP      "RADIO SETUP"
#define TR_MENUTRAINER         "TRAINER"
#define TR_MENUVERSION         "VERSION"
#define TR_MENUDIAG            "SWITCHES"
#define TR_MENUANA             "ANAS"
#define TR_MENUCALIBRATION     "CALIBRATION"
#define TR_TRIMS2OFFSETS     "\006Trims => Subtrims"
#define TR_MENUMODELSEL        "MODELSEL"
#define TR_MENUSETUP           "SETUP"
#define TR_MENUFLIGHTPHASES    "FLIGHT MODES"
#define TR_MENUFLIGHTPHASE     "FLIGHT MODE"
#define TR_MENUHELISETUP       "HELI SETUP"
#define TR_MENUINPUTS        "STICKS"
#define TR_MENULIMITS        "SERVOS"
#define TR_MENUCURVES          "CURVES"
#define TR_MENUCURVE           "CURVE"
#define TR_MENULOGICALSWITCHES "LOGICAL SWITCHES"
#define TR_MENUCUSTOMFUNC      "SPECIAL FUNCTIONS"
#define TR_MENUTELEMETRY       "TELEMETRY"
#define TR_MENUTEMPLATES       "TEMPLATES"
#define TR_MENUSTAT            "STATS"
#define TR_MENUDEBUG           "DEBUG"
#define TR_RXNUM             "RxNum"
#define TR_LIMIT               INDENT "Limit"
#define TR_MINRSSI             "Min Rssi"
#define TR_LATITUDE            "Latitude"
#define TR_LONGITUDE           "Longitude"
#define TR_GPSCOORD            "GPS Coords"
#define TR_VARIO               "Vario"
#define TR_POWEROFF            "\006SHUT DOWN ?"
#define TR_SHUTDOWN            "SHUTTING DOWN"
#define TR_SAVEMODEL           "Saving model settings"
#define TR_BATT_CALIB          "Battery Calib"
#define TR_VOLTAGE             INDENT "Voltage"
#define TR_CURRENT             INDENT "Current"
#define TR_SELECT_MODEL        "Select Model"
#define TR_CREATE_MODEL        "Create Model"
#define TR_COPY_MODEL          "Copy Model"
#define TR_MOVE_MODEL          "Move Model"
#define TR_BACKUP_MODEL        "Backup Model"
#define TR_DELETE_MODEL        "Delete Model"
#define TR_RESTORE_MODEL       "Restore Model"
#define TR_SDCARD_ERROR        "SD Card Error"
#define TR_NO_SDCARD           "No SD Card"
#define TR_INCOMPATIBLE        "Incompatible"
#define TR_WARNING             "WARNING"
#define TR_EEPROMWARN          "EEPROM"
#define TR_THROTTLEWARN        "THROTTLE"
#define TR_ALARMSWARN          "ALARMS"
#define TR_SWITCHWARN          "SWITCH"
#define TR_INVERT_THR          "Invert Thr?"
#define TR_SPEAKER_VOLUME      INDENT "Volume"
#define TR_FUNC                "Func"
#define TR_DELAY               "Delay"
#define TR_SD_CARD             "SD CARD"
#define TR_NO_MODELS_ON_SD     "No Models" BREAKSPACE "on SD"
#define TR_PLAY_FILE           "Play"
#define TR_DELETE_FILE         "Delete"
#define TR_COPY_FILE           "Copy"
#define TR_RENAME_FILE         "Rename"
#define TR_REMOVED             " removed"
#define TR_SD_INFO             "Information"
#define TR_NA                  "N/A"
#define TR_TIME                "Time"
#if defined(IMPERIAL_UNITS)
  #define TR_TXTEMP              "Temp. TX\037\164@F"
#else
  #define TR_TXTEMP              "Temp. TX\037\164@C"
#endif
#define TR_SD_INFO_TITLE       "SD INFO"
#define TR_SD_TYPE             "Type:"
#define TR_SD_SIZE             "Size:"
#define TR_TYPE                INDENT "Type"
#define TR_GLOBAL_VARS         "Global Variables"
#define TR_GLOBAL_V            "GLOBAL V."
#define TR_GLOBAL_VAR          "Global Variable"
#define TR_OWN                 "Own"
#define TR_DATE                "Date"
#define TR_ROTARY_ENCODER      "R.Encs"
#define TR_EDIT                "Edit"
#define TR_INSERT_BEFORE       "Insert Before"
#define TR_INSERT_AFTER        "Insert After"
#define TR_COPY                "Copy"
#define TR_MOVE                "Move"
#define TR_PASTE               "Paste"
#define TR_DELETE              "Delete"
#define TR_INSERT              "Insert"
#define TR_RESET_FLIGHT        "Reset Flight"
#define TR_RESET_TIMER1        "Reset Timer1"
#define TR_RESET_TIMER2        "Reset Timer2"
#define TR_RESET_TELEMETRY     "Reset Telemetry"
#define TR_STATISTICS          "Statistics"
#define TR_SAVE_TIMERS         "Save Timers"
#define TR_SPEAKER             INDENT "Speaker"
#define TR_BUZZER              INDENT "Buzzer"
#define TR_MODULE_BIND         "[Bnd]"
#define TR_MODULE_RANGE        "[Prt]"
#define TR_RESET_BTN           "[Reset]"
#define TR_SET                 "[Set]"
#define TR_NUMCH               INDENT "Num channels"
#define TR_UBIND               INDENT "Unbind"
#define TR_RESET               "Reset"
#define TR_FAS_OFFSET          INDENT "FAS Ofs"
#if defined(X_ANY) || defined(BLUETOOTH)
  #define TR_X_ANY                        "X ANY"
  #define TR_ACTIVED                      "Active"
  #define TR_NUMBER                       "Number"
  #define TR_CHANNEL                      "Channel "
  #define TR_NB_REPEAT                    "Nb repeat "
  #define LEN_SWITCHES_VALUES             "\005"
  #define TR_SWITCHES_VALUES              "Sw.--""L1-L4""L1-L8""Sw.4 ""Sw.8 ""Sw.16"
  #define TR_ANGLE_SENSOR                 "0:360"
  #define TR_PROP                         "Prop."
  #define LEN_XANY_EXPO                   "\005"
  #define TR_XANY_EXPO                    "0%\0  ""25%\0 ""37.5%""50%\0 "
#endif
#if defined(BLUETOOTH)
  #define TR_BLUETOOTH                     "BLUETOOTH"
  #define TR_NOBLUETOOTH                   "\3NO BLUETOOTH"
  #define TR_CONNECTED                     "\036\5CONECTEd"
  #define TR_BT_ROLE                       "Role"
  #define TR_BT_PIN                        "Pin"
  #define TR_BT_M_S                        "\006""Slave\0""Master"
  #define TR_BT_PAIR                       "Pair"
  #define TR_AUTOCON                       "Auto-con."
  #define TR_RESCANN                       "Re-Scan"
#endif

#if defined(SCC)
  #define TR_SCC                            "CHANNEL CHANGER"
  #define TR_SCC_CURCHANNELLBL              "Actual Channel"
  #define TR_SCC_NEWCHANNELLBL              "Select Channel"
  #define TR_SCC_SBUSSWEEPTESTLBL           "SBus Sweep Test"
#endif
