Ingwie/OpenAVRc_Dev/OpenAVRc/translations/fr.h

/*
**************************************************************************
*                                                                        *
*                 ____                ___ _   _____                      *
*                / __ \___  ___ ___  / _ | | / / _ \____                 *
*               / /_/ / _ \/ -_) _ \/ __ | |/ / , _/ __/                 *
*               \____/ .__/\__/_//_/_/ |_|___/_/|_|\__/                  *
*                   /_/                                                  *
*                                                                        *
*              This file is part of the OpenAVRc project.                *
*                                                                        *
*                         Based on code(s) named :                       *
*             OpenTx - https://github.com/opentx/opentx                  *
*             Deviation - https://www.deviationtx.com/                   *
*                                                                        *
*                Only AVR code here for visibility ;-)                   *
*                                                                        *
*   OpenAVRc is free software: you can redistribute it and/or modify     *
*   it under the terms of the GNU General Public License as published by *
*   the Free Software Foundation, either version 2 of the License, or    *
*   (at your option) any later version.                                  *
*                                                                        *
*   OpenAVRc is distributed in the hope that it will be useful,          *
*   but WITHOUT ANY WARRANTY; without even the implied warranty of       *
*   MERCHANTABILITY or FITNESS FOR A PARTICULAR PURPOSE.  See the        *
*   GNU General Public License for more details.                         *
*                                                                        *
*       License GPLv2: http://www.gnu.org/licenses/gpl-2.0.html          *
*                                                                        *
**************************************************************************
*/
/* Formatting octal codes available in TR_ strings:
*  \037\x           -sets LCD x-coord (x value in octal)
*  \036             -newline
*  \001 to \034     -extended spacing (value * FW/2)
*  \0               -ends current string
*/

/* NON ZERO TERMINATED STRINGS */
#define LEN_OFFON              "\003"
#define TR_OFFON               "OFF""ON\0"
#define LEN_MMMINV             "\003"
#define TR_MMMINV              "---""INV"
#define LEN_NCHANNELS          "\004"
#define TR_NCHANNELS           "\0014CH\0016CH\0018CH10CH12CH14CH16CH"
#define LEN_VBEEPMODE          "\005"
#define TR_VBEEPMODE           "Aucun""Alarm""NoKey""Tout\0"
#define LEN_VRENAVIG           "\003"
#define TR_VRENAVIG            "NonREaREb"
#define LEN_VBLMODE            "\004"
#define TR_VBLMODE             "OFF\0""Btns""Ctrl""Tous""ON\0"
#define LEN_TRNMODE            "\003"
#define TR_TRNMODE             "OFF"" +="" :="
#define LEN_TRNCHN             "\003"
#define TR_TRNCHN              "CH1CH2CH3CH4"
#define LEN_VPERSISTENT        "\014"
#define TR_VPERSISTENT         "OFF\0        ""Vol\0        ""Reset Manuel"
#define LEN_DSM_PROTOCOLS      "\004"
#define TR_DSM_PROTOCOLS       "LP45""DSM2""DSMX"
#define LEN_VTRIMINC           "\006"
#define TR_VTRIMINC            "Expo\0 ""ExFin\0""Fin\0  ""Moyen\0""Gros\0 "
#define LEN_CURVE_TYPES        "\010"
#define TR_CURVE_TYPES         "Standard""Libre\0"
#define LEN_RETA123            "\001"
#define TR_RETA123           "DPGA123ab"

#if defined(PWM_BACKLIGHT)
  #define TR_BLONBRIGHTNESS     INDENT "Lumin. ON"
  #define TR_BLOFFBRIGHTNESS    INDENT "Lumin. OFF"
#endif
#if (SERIAL_PROTOCOL==DSM)
  #define TR_DSM2              "LP45\0 ""DSM2\0 ""DSMX\0 "
#else
  #define TR_DSM2
#endif

#define TR_SPIM               "SPIRfMod"
#define TR_RFPOWER INDENT     "Puissance RF"

#define TR_PERIOD                INDENT "P\200riode"
#define TR_MODULE              "Module"
#define TR_SUBPROTO            "Sous Proto."
#define TR_RFTUNEFINE          INDENT "Ajust.fr\200q"
#define TR_TELEMETRY           "T\200l\200m\200trie"
#define TR_MULTI_VIDFREQ       INDENT "Fr\200q. vid\200o"
#define TR_MULTI_RFPOWER       INDENT "Puiss. RF"
#define TR_MULTI_OPTION        INDENT "Option"
#define TR_MULTI_SERVOFREQ     INDENT "Fr\200q.servo"
#define TR_AUTOBIND            INDENT "Bind auto"
#define TR_MULTI_DSM_AUTODTECT INDENT "Autod\200t."
#define TR_MULTI_LOWPOWER      INDENT "Basse puis."
#define TR_MULTI_FIXEDID               "ID fixe"
#define TR_MULTI_MAX_THROW             "Max. Throw"
#define TR_MULTI_RFCHAN                "Sel. Voie"
#define TR_MULTI_OUTPUT                "Sortie"

#define LEN_VCURVEFUNC         "\003"
#define TR_VCURVEFUNC          "---""x>0""x<0""|x|""f>0""f<0""|f|"
#define LEN_VMLTPX             "\010"
#define TR_VMLTPX              "Ajoute\0 ""Multipl.""Remplace"
#define LEN_VMLTPX2            "\002"
#define TR_VMLTPX2             "+=""*="":="
#define LEN_VMIXTRIMS          "\003"
#define TR_VMIXTRIMS           "OFF""ON\0""Dir""Prf""Gaz""Ail"
#define TR_CSWTIMER          "Temp\0"
#define TR_CSWSTICKY         "Bist\0"
#define TR_CSWRANGE
#define TR_CSWSTAY
#define LEN_VCSWFUNC           "\005"
#define TR_VCSWFUNC            "---\0 " "a=x\0 " "a\173x\0 ""a>x\0 ""a<x\0 " TR_CSWRANGE "|a|>x""|a|<x""ET\0  ""OU\0  ""OUX\0 " TR_CSWSTAY "a=b\0 ""a>b\0 ""a<b\0 ""^}x\0 ""|^|}x" TR_CSWTIMER TR_CSWSTICKY
#define LEN_VFSWFUNC           "\015"
#if defined(VARIO)
  #define TR_VVARIO            "Vario\0       "
#else
  #define TR_VVARIO            "[Vario]\0     "
#endif
#if defined(AUDIO)
  #define TR_SOUND             "Jouer son\0   "
#else
  #define TR_SOUND             "Bip\0         "
#endif
#if defined(HAPTIC)
  #define TR_HAPTIC            "Vibreur\0     "
#else
  #define TR_HAPTIC            "[Vibreur]\0   "
#endif
#if defined(VOICE)
  #define TR_PLAY_TRACK      "Jouer fich\0  "
  #define TR_PLAY_BOTH         "Jouer les 2\0 "
  #define TR_PLAY_VALUE        "Lire valeur\0 "
#else
  #define TR_PLAY_TRACK        "[Jouer fich.]"
  #define TR_PLAY_BOTH         "[Jouer les 2]"
  #define TR_PLAY_VALUE        "[Lire valeur]"
#endif
#if defined(SDCARD)
  #define TR_SDCLOGS           "Logs SD\0     "
#else
  #define TR_SDCLOGS           "[Logs SD]\0   "
#endif
#if defined(GVARS)
  #define TR_ADJUST_GVAR       "Ajuster\0     "
#else
  #define TR_ADJUST_GVAR       "[AjusteGV]\0  "
#endif

#if   defined(OVERRIDE_CHANNEL_FUNCTION)
  #define TR_SF_SAFETY        "Rempl.\0      "
#else
  #define TR_SF_SAFETY        "---\0         "
#endif

#define TR_VFSWFUNC          TR_SF_SAFETY "Ecolage\0     ""Trim instant.""Remise \202 0\0  " TR_ADJUST_GVAR TR_SOUND TR_PLAY_TRACK TR_PLAY_BOTH TR_PLAY_VALUE TR_VVARIO TR_HAPTIC TR_SDCLOGS "R\200tro\200cl.\0   "
#define LEN_VFSWRESET          "\004"
#if defined(FRSKY)
  #define TR_FSW_RESET_TELEM   "Telm"
  #define TR_MODELISON         INDENT "Le mod\201le est allum\200"
#else
  #define TR_FSW_RESET_TELEM
#endif
#define TR_FSW_RESET_TIMERS  "Chr1""Chr2"
#define TR_FSW_RESET_ROTENC  "REa\0""REb\0"
#define TR_VFSWRESET           TR_FSW_RESET_TIMERS "Tout" TR_FSW_RESET_TELEM TR_FSW_RESET_ROTENC
#define LEN_FUNCSOUNDS         "\004"
#define TR_FUNCSOUNDS          "Bp1\0""Bp2\0""Bp3\0""Wrn1""Wrn2""Chee""Rata""Tick""Sirn""Ring""SciF""Robt""Chrp""Tada""Crck""Alrm"
#define LEN_VTELEMCHNS         "\004"
#define TR_TELEM_RESERVE
#define TR_TELEM_TIME
#define TR_SWR
#define TR_RX_BATT
#define TR_A3_A4
#define TR_A3_A4_MIN
#define TR_ASPD_MAX            "ViA+"
#define TR_TELEM_RSSI_RX     "Rx\0 "
#define TR_TELEM_TIMERS      "Chr1""Chr2"
#define TR_VTELEMCHNS        "---\0""Batt" TR_TELEM_TIME TR_TELEM_RESERVE TR_TELEM_RESERVE TR_TELEM_RESERVE TR_TELEM_RESERVE TR_TELEM_RESERVE TR_TELEM_TIMERS TR_SWR "Tx\0 " TR_TELEM_RSSI_RX TR_RX_BATT "A1\0 ""A2\0 " TR_A3_A4 "Alt\0""Rpm\0""Carb""T1\0 ""T2\0 ""Vit\0""Dist""AltG""Elem""Velm""Vfas""Cour""Cnsm""Puis""AccX""AccY""AccZ""Cap\0""VitV""VitA""dET\0" TR_TELEM_RESERVE TR_TELEM_RESERVE TR_TELEM_RESERVE TR_TELEM_RESERVE TR_TELEM_RESERVE "A1-\0""A2-\0" TR_A3_A4_MIN "Alt-""Alt+""Rpm+""T1+\0""T2+\0""Vit+""Dst+" TR_ASPD_MAX "Elm-""Els-""Vfs-""Cur+""Pui+" TR_TELEM_RESERVE TR_TELEM_RESERVE TR_TELEM_RESERVE TR_TELEM_RESERVE TR_TELEM_RESERVE "Acc\0""Tmps"
#define LENGTH_UNIT_IMP        "ft\0"
#define SPEED_UNIT_IMP         "mph"
#define LENGTH_UNIT_METR       "m\0 "
#define SPEED_UNIT_METR        "kmh"
#if defined(IMPERIAL_UNITS)
  #define LENGTH_UNIT        LENGTH_UNIT_IMP
  #define SPEED_UNIT         SPEED_UNIT_IMP
#else
  #define LENGTH_UNIT        LENGTH_UNIT_METR
  #define SPEED_UNIT         SPEED_UNIT_METR
#endif
#define LEN_VTELEMUNIT       "\003"
#define TR_VTELEMUNIT        "V\0 ""A\0 ""m/s""-\0 " SPEED_UNIT LENGTH_UNIT "@\0 ""%\0 ""mA\0""mAh""W\0 "
#define STR_V                  (STR_VTELEMUNIT+1)
#define STR_A                  (STR_VTELEMUNIT+4)
#define LEN_VTELPROTO          "\007"
#define TR_VTELPROTO           "Aucun  ""Hub\0   ""WSHHigh""S.Port\0""iBus\0  "
#define LEN_AMPSRC           "\003"
#define TR_AMPSRC            "---""A1\0""A2\0""FAS""Cel"
#define LEN_VARIOSRC           "\005"
#if defined(FRSKY_SPORT)
  #define TR_VARIOSRC          "Vario""A1\0  ""A2\0  ""dTE\0 "
#else
  #define TR_VARIOSRC          "Alti\0""Alti+""Vario""A1\0  ""A2\0"
#endif
#define LEN_VTELEMSCREENTYPE "\004"
#define TR_VTELEMSCREENTYPE  "Val.""Bars"
#define LEN_GPSFORMAT          "\004"
#define TR_GPSFORMAT           "DMS\0""NMEA"
#define LEN2_VTEMPLATES        15
#define LEN_VTEMPLATES         "\017"
#define TR_VTEMPLATES          "Suppr Mixages\0 ""4 Voies simple\0""Coupure Gaz\0   ""Empennage V\0   ""Elevon\\Delta\0  ""eCCPM\0         ""Conf. H\200lico\0  ""Test Servo\0    "
#define LEN_VSWASHTYPE         "\004"
#define TR_VSWASHTYPE          "--- ""120 ""120X""140 ""90\0"
#define LEN_VKEYS              "\005"
#define TR_VKEYS               "Menu\0""Exit\0""Bas\0 ""Haut\0""Droit""Gauch"
#define LEN_VRENCODERS         "\003"
#define TR_VRENCODERS          "REa""REb"
#define TR_STICKS_VSRCRAW      "Dir\0""Prf\0""Gaz\0""Ail\0"
#define TR_TRIMS_VSRCRAW       "TrmD""TrmP""TrmG""TrmA"
#define TR_POTS_VSRCRAW      "P1\0 ""P2\0 ""P3\0 "
#define TR_SW_VSRCRAW        "3POS"
#define TR_9X_3POS_SWITCHES  "ID0""ID1""ID2"
#define TR_LOGICALSW         "L1\0""L2\0""L3\0""L4\0""L5\0""L6\0""L7\0""L8\0""L9\0""L10""L11""L12""L13""L14""L15""L16""L17""L18""L19""L20"
#define TR_TRIMS_SWITCHES      "tDg""tDd""tPb""tPh""tGb""tGh""tAg""tAd"
#define TR_ROTARY_ENCODERS   "REa\0""REb\0"
#define TR_ROTENC_SWITCHES   "REA""REB""REN"
#define TR_PHYS_SWITCHES     "THR""RUD""ELE""AIL""GEA""TRN"
#define TR_ON_ONE_SWITCHES     "ON\0""Un"
#define TR_EXTRA_3POS_SWITCHES  "XD0""XD1""XD2"
#define LEN_VSRCRAW            "\004"
#define LEN_VSWITCHES          "\003"
#define TR_VSWITCHES         "---" TR_9X_3POS_SWITCHES TR_PHYS_SWITCHES TR_TRIMS_SWITCHES TR_ROTENC_SWITCHES TR_EXTRA_3POS_SWITCHES TR_LOGICALSW TR_ON_ONE_SWITCHES
#if defined(HELI)
  #define TR_CYC_VSRCRAW       "CYC1""CYC2""CYC3"
#else
  #define TR_CYC_VSRCRAW       "[C1]""[C2]""[C3]"
#endif
#define TR_EXTRA_VSRCRAW
#define TR_VSRCRAW             "---\0" TR_STICKS_VSRCRAW TR_POTS_VSRCRAW TR_ROTARY_ENCODERS "MAX\0" TR_CYC_VSRCRAW TR_TRIMS_VSRCRAW TR_SW_VSRCRAW TR_EXTRA_VSRCRAW
#define LEN_VTMRMODES          "\003"
#define TR_VTMRMODES           "OFF""ON\0""GZs""GZ%""GZt"

/* ZERO TERMINATED STRINGS */
#define INDENT                 "\001"
#define LEN_INDENT             1
#define INDENT_WIDTH           (FW/2)
#define BREAKSPACE           " "
#define TR_ENTER             "[MENU]"
#define TR_EXIT                "[EXIT]"
#define TR_POPUPS            TR_ENTER "\010" TR_EXIT
#define OFS_EXIT             sizeof(TR_ENTER)
#define TR_MENUWHENDONE        CENTER "\006" TR_ENTER " QUAND PRET"
#define TR_FREE                "disp"
#define TR_DELETEMODEL         "SUPPRIMER" BREAKSPACE "MODELE"
#define TR_COPYINGMODEL        "Copie..."
#define TR_MOVINGMODEL         "D\200placement..."
#define TR_LOADINGMODEL        "Chargement..."
#define TR_NAME                "Nom"
#define TR_TIMER               "Chrono "
#define TR_ELIMITS             "Limites \200t."
#define TR_ETRIMS              "Trims \200t."
#define TR_TRIMINC             "Pas Trim"
#define TR_TTRACE              "Source Gaz"
#define TR_TSWITCH             "Switch Gaz"
#define TR_TTRIM               "Trim gaz"
#define TR_BEEPCTR             "Bips centr"
#define TR_PROTO               INDENT "Protocole"
#define TR_PPMFRAME          "Trame PPM"
#define TR_MS                  "ms"
#define TR_SWITCH              "Inter"
#define TR_TRIMS               "Trims"
#define TR_FADEIN              "Fondu ON"
#define TR_FADEOUT             "Fondu OFF"
#define TR_DEFAULT             "(d\200faut)"
#define TR_CHECKTRIMS          "\006V\200rif\012Trims"
#define OFS_CHECKTRIMS         (9*FW)
#define TR_SWASHTYPE           "Type de Plat."
#define TR_COLLECTIVE          "Collectif"
#define TR_SWASHRING           "Limite Cycl."
#define TR_ELEDIRECTION        "Inv. longitud."
#define TR_AILDIRECTION        "Inv. lat\200ral"
#define TR_COLDIRECTION        "Inv. collectif"
#define TR_MODE                INDENT "Mode"
#define TR_NOFREEEXPO          "Max expos atteint!"
#define TR_NOFREEMIXER         "Max mixages atteint!"
#define TR_INSERTMIX           "INSERER MIXAGE"
#define TR_EDITMIX             "EDITER MIXAGE"
#define TR_SOURCE              INDENT "Source"
#define TR_WEIGHT              "Ratio"
#define TR_EXPO                "Expo"
#define TR_SIDE                "Cot\200"
#define TR_DIFFERENTIAL        "Diff\200rentiel"
#define TR_OFFSET              INDENT "D\200calage"
#define TR_TRIM                "Trim"
#define TR_DREX                "DRex"
#define DREX_CHBOX_OFFSET      30
#define TR_CURVE               "Courbe"
#define TR_FLMODE              "Phase"
#define TR_MIXWARNING          "Alerte"
#define TR_OFF                 "OFF"
#define TR_MULTPX              "Op\200ration"
#define TR_DELAYDOWN           "Retard bas"
#define TR_DELAYUP             "Retard haut"
#define TR_SLOWDOWN            "Ralenti bas"
#define TR_SLOWUP              "Ralenti haut"
#define TR_MIXER               "MIXEUR"
#define TR_CV                  "CB"
#define TR_GV                  "VG"
#define TR_ACHANNEL            "A"
#define TR_RANGE               INDENT "Plage"
#define TR_ALARM               INDENT "Alarme"
#define TR_USRDATA             "Donn\200es"
#define TR_BLADES              INDENT "Pales"
#define TR_SCREEN              "Ecran "
#define TR_SOUND_LABEL         "Son"
#define TR_LENGTH              INDENT "Dur\200e"
#define TR_BEEP_LENGTH         INDENT "Dur\200e bips"
#define TR_SPKRPITCH           INDENT "Tonalit\200"
#define TR_HAPTIC_LABEL        "Vibreur"
#define TR_HAPTICSTRENGTH      INDENT "Force"
#define TR_CONTRAST            "Contraste"
#define TR_ALARMS_LABEL        "Alarmes"
#define TR_BATTERY_RANGE       "Plage batterie"
#define TR_BATTERYWARNING      INDENT "Batterie"
#define TR_INACTIVITYALARM     INDENT "Inactivit\200"
#define TR_MEMORYWARNING       INDENT "M\200moire pleine"
#define TR_ALARMWARNING        INDENT "Silence"
#define TR_RENAVIG             "Navig EncRot"
#define TR_MINUTEBEEP          INDENT "Bip min."
#define TR_BEEPCOUNTDOWN       INDENT "Bip fin"
#define TR_PERSISTENT          INDENT "Persist."
#define TR_BACKLIGHT_LABEL     "R\200tro\200clairage"
#define TR_BLDELAY             INDENT "Dur\200e"
#define TR_SPLASHSCREEN        "Logo d'accueil"
#define TR_THROTTLEWARNING     "Alerte gaz"
#define TR_SWITCHWARNING       "Alerte int"
#define TR_TIMEZONE            "Fuseau horaire"
#define TR_ADJUST_RTC          "Ajust. heure auto"
#define TR_GPS                 "GPS"
#define TR_RXCHANNELORD        "Ordre voies RX"
#define TR_STICKS              "Manches"
#define TR_POTS                "Pot."
#define TR_SLAVE               "El\201ve"
#define TR_MODESRC             "Mode\006% Source"
#define TR_MULTIPLIER          "Multiplieur"
#define TR_CAL                 "Cal"
#define TR_VTRIM               "Trim- +"
#define TR_MENUTOSTART       CENTER"\006" TR_ENTER " POUR DEBUT"
#define TR_SETMIDPOINT       CENTER"\010REGLER NEUTRES"
#define TR_MOVESTICKSPOTS    CENTER"\004BOUGER STICKS/POTS"
#define TR_RXBATT              "Batt.RX"
#define TR_TXnRX               "Tx:\0Rx:"
#define OFS_RX                 4
#define TR_ACCEL               "Acc:"
#define TR_NODATA              CENTER "NO DATA"
#define TR_TOTTM1TM2THRTHP     "\037\146SES\036TM1\037\146TM2\036GAZ\037\146GZ%"
#define TR_US                  "us"
#define TR_MENUTORESET         CENTER TR_ENTER" pour reset"
#define TR_PPM_TRAINER         "TR"
#define TR_CH                  "CH"
#define TR_MODEL               "MODELE"
#define TR_FP                  "PV"
#define TR_MIX                 "MIX"
#define TR_EEPROMLOWMEM        "EEPROM pleine!"
#define TR_ALERT               "\014ALERTE"
#define TR_PRESSANYKEYTOSKIP   "Touche pour ignorer"
#define TR_THROTTLENOTIDLE     "Gaz pas \202 z\200ro"
#define TR_ALARMSDISABLED      "Alarmes D\200sactiv\200es"
#define TR_PRESSANYKEY         "Touche pour continuer"
#define TR_BADEEPROMDATA       "EEPROM corrompue"
#define TR_EEPROMFORMATTING    "Formatage EEPROM"
#define TR_EEPROMOVERFLOW      "D\200passement EEPROM"
#define TR_MENURADIOSETUP      "CONFIG RADIO"
#define TR_MENUTRAINER         "ECOLAGE"
#define TR_MENUVERSION         "VERSION"
#define TR_MENUDIAG            "INTERS"
#define TR_MENUANA             "ANAS"
#define TR_MENUCALIBRATION     "CALIBRATION"
#define TR_TRIMS2OFFSETS       "\005Trims => Subtrims"
#define TR_MENUMODELSEL        "MODELES"
#define TR_MENUSETUP           "CONF. MODELE"
#define TR_MENUFLIGHTPHASE     "PHASE DE VOL"
#define TR_MENUFLIGHTPHASES    "PHASES DE VOL"
#define TR_MENUHELISETUP       "CONF.HELI"
#define TR_MENUINPUTS        "DR/EXPO"
#define TR_MENULIMITS        "LIMITES"
#define TR_MENUCURVES          "COURBES"
#define TR_MENUCURVE           "COURBE"
#define TR_MENULOGICALSWITCHES "INTERS LOG."
#define TR_MENUCUSTOMFUNC      "FONCTIONS SPEC."
#define TR_MENUTELEMETRY       "TELEMESURE"
#define TR_MENUTEMPLATES       "GABARITS"
#define TR_MENUSTAT            "STATS"
#define TR_MENUDEBUG           "DEBUG"
#define TR_RXNUM               INDENT "NumRx"
#define TR_LIMIT               INDENT "Limite"
#define TR_MINRSSI             "RSSI Min."
#define TR_LATITUDE            "Latitude"
#define TR_LONGITUDE           "Longitude"
#define TR_GPSCOORD            "Coordonn\200es"
#define TR_VARIO               "Vario"
#define TR_POWEROFF            "\006ETEINDRE ?"
#define TR_SHUTDOWN            "\3ARRET EN COURS"
#define TR_SAVEMODEL           "Sauvegarde ..."
#define TR_BATT_CALIB          "Calib. Batterie"
#define TR_VOLTAGE             INDENT "Tension"
#define TR_CURRENT             INDENT "Courant"
#define TR_SELECT_MODEL        "S\200lect. Mod\201le"
#define TR_CREATE_MODEL        "Cr\200er Mod\201le"
#define TR_COPY_MODEL          "Copier Mod\201le"
#define TR_MOVE_MODEL          "D\200placer Mod\201le"
#define TR_BACKUP_MODEL        "Archiver Mod\201le"
#define TR_DELETE_MODEL        "Supprimer Mod\201le"
#define TR_RESTORE_MODEL       "Restaurer Mod\201le"
#define TR_SDCARD_ERROR        "Erreur carte SD"
#define TR_NO_SDCARD           "Carte SD muette"
#define TR_INCOMPATIBLE        "Incompatible"
#define TR_WARNING             "ALERTE"
#define TR_EEPROMWARN          "EEPROM"
#define TR_THROTTLEWARN        "GAZ"
#define TR_ALARMSWARN          "SON"
#define TR_SWITCHWARN          "INTERS"
#define TR_INVERT_THR          "Inverser Gaz?"
#define TR_SPEAKER_VOLUME      INDENT "Volume"
#define TR_FUNC                "Fonc"
#define TR_DELAY               "D\200lai"
#define TR_SD_CARD             "Carte SD"
#define TR_NO_MODELS_ON_SD     "Aucun mod\201le SD"
#define TR_PLAY_FILE           "Lire"
#define TR_DELETE_FILE         "Supprimer"
#define TR_COPY_FILE           "Copier"
#define TR_RENAME_FILE         "Renommer"
#define TR_REMOVED             " supprim\200"
#define TR_SD_INFO             "Information"
#define TR_NA                  "N/D"
#define TR_TIME                "Heure"
#if defined(IMPERIAL_UNITS)
  #define TR_TXTEMP              "Temp. radio\037\164@F"
#else
  #define TR_TXTEMP              "Temp. radio\037\164@C"
#endif
#define TR_SD_INFO_TITLE       "INFO SD"
#define TR_SD_TYPE             "Type:"
#define TR_SD_SIZE             "Taille:"
#define TR_TYPE                INDENT "Type"
#define TR_GLOBAL_VARS         "Variables Globales"
#define TR_GLOBAL_V            "V. GLOBALES"
#define TR_GLOBAL_VAR          "Variable globale"
#define TR_OWN                 "Pers"
#define TR_DATE                "Date"
#define TR_ROTARY_ENCODER      "Enc.Rot."
#define TR_EDIT                "Editer"
#define TR_INSERT_BEFORE       "Ins\200rer avant"
#define TR_INSERT_AFTER        "Ins\200rer apr\201s"
#define TR_COPY                "Copier"
#define TR_MOVE                "D\200placer"
#define TR_PASTE               "Coller"
#define TR_DELETE              "Supprimer"
#define TR_INSERT              "Ins\200rer"
#define TR_RESET_FLIGHT        "R\200init. vol"
#define TR_RESET_TIMER1        "R\200init. Timer1"
#define TR_RESET_TIMER2        "R\200init. Timer2"
#define TR_RESET_TELEMETRY     "R\200init. T\200l\200m."
#define TR_STATISTICS          "Statistiques"
#define TR_SAVE_TIMERS         "Garder Timers"
#define TR_SPEAKER             INDENT "Haut-p."
#define TR_BUZZER              INDENT "Bipeur"
#define TR_MODULE_BIND         "[Bnd]"
#define TR_MODULE_RANGE        "[Prt]"
#define TR_RESET_BTN           "[RAZ]"
#define TR_SET                 "[D\200f]"
#define TR_NUMCH               INDENT "Num. voies"
#define TR_UBIND               INDENT "Sup. Bind"
#define TR_RESET               "R\200initialiser"
#define TR_FAS_OFFSET          INDENT "Corr FAS"
#if defined(X_ANY) || defined(BLUETOOTH)
  #define TR_X_ANY                        "X ANY"
  #define TR_ACTIVED                      "Actif"
  #define TR_NUMBER                       "Num\200ro"
  #define TR_CHANNEL                      "Voie "
  #define TR_NB_REPEAT                    "Nb r\200p\200tition "
  #define LEN_SWITCHES_VALUES             "\005"
  #define TR_SWITCHES_VALUES              "Sw.--""L1-L4""L1-L8""Sw.4 ""Sw.8 ""Sw.16"
  #define TR_ANGLE_SENSOR                 "0:360"
  #define TR_PROP                         "Prop."
  #define LEN_XANY_EXPO                   "\005"
  #define TR_XANY_EXPO                    "0%\0  ""25%\0 ""37.5%""50%\0 "
#endif
#if defined(BLUETOOTH)
  #define TR_BLUETOOTH                     "BLUETOOTH"
  #define TR_NOBLUETOOTH                   "BLUETOOTH MUET"
  #define TR_CONNECTED                     "\036\6CONECTE"
  #define TR_BT_ROLE                       "Role"
  #define TR_BT_PIN                        "Pin"
  #define TR_BT_M_S                        "\006""Slave\0""Master"
  #define TR_BT_PAIR                       "Pair"
  #define TR_AUTOCON                       "Auto-con."
  #define TR_RESCANN                       "Re-Scan"
#endif

#if defined(SCC)
  #define TR_SCC                            "CHANGEUR DE CANAL"
  #define TR_SCC_CURCHANNELLBL              "Canal actuel"
  #define TR_SCC_NEWCHANNELLBL              "Canal demand\200"
  #define TR_SCC_SBUSSWEEPTESTLBL           "Test lecture SBus"
#endif
