Ingwie/OpenAVRc_Dev/OpenAVRc/mixer.cpp

 /*
 **************************************************************************
 *                                                                        *
 *                 ____                ___ _   _____                      *
 *                / __ \___  ___ ___  / _ | | / / _ \____                 *
 *               / /_/ / _ \/ -_) _ \/ __ | |/ / , _/ __/                 *
 *               \____/ .__/\__/_//_/_/ |_|___/_/|_|\__/                  *
 *                   /_/                                                  *
 *                                                                        *
 *              This file is part of the OpenAVRc project.                *
 *                                                                        *
 *                         Based on code(s) named :                       *
 *             OpenTx - https://github.com/opentx/opentx                  *
 *             Deviation - https://www.deviationtx.com/                   *
 *                                                                        *
 *                Only AVR code here for visibility ;-)                   *
 *                                                                        *
 *   OpenAVRc is free software: you can redistribute it and/or modify     *
 *   it under the terms of the GNU General Public License as published by *
 *   the Free Software Foundation, either version 2 of the License, or    *
 *   (at your option) any later version.                                  *
 *                                                                        *
 *   OpenAVRc is distributed in the hope that it will be useful,          *
 *   but WITHOUT ANY WARRANTY; without even the implied warranty of       *
 *   MERCHANTABILITY or FITNESS FOR A PARTICULAR PURPOSE.  See the        *
 *   GNU General Public License for more details.                         *
 *                                                                        *
 *       License GPLv2: http://www.gnu.org/licenses/gpl-2.0.html          *
 *                                                                        *
 **************************************************************************
*/


#include "OpenAVRc.h"
#include "timers.h"

int16_t  rawAnas[NUM_STICKS] = {0};
int16_t  anas [NUM_STICKS] = {0};
int16_t  trims[NUM_STICKS] = {0};
int32_t  chans[NUM_CHNOUT] = {0};
BeepANACenter bpanaCenter = 0;

MixVal   mixVal[MAX_MIXERS];

uint8_t mixWarning;

int16_t calibratedStick[NUM_STICKS+NUM_POTS];
int16_t channelOutputs[NUM_CHNOUT] = {0};
int16_t ex_chans[NUM_CHNOUT] = {0}; // Outputs (before LIMITS) of the last perMain;

#if defined(HELI)
int16_t cyc_anas[3] = {0};
#endif

void applyExpos(int16_t *anas, uint8_t mode APPLY_EXPOS_EXTRA_PARAMS)
{
  int16_t anas2[NUM_STICKS]; // values before expo, to ensure same expo base when multiple expo lines are used
  memcpy(anas2, anas, sizeof(anas2));

  int8_t cur_chn = -1;

  for (uint8_t i=0; i<MAX_EXPOS; i++) {
#if defined(BOLD_FONT)
    if (mode==e_perout_mode_normal) mixVal[i].activeExpo = false;
#endif
    ExpoData * ed = expoAddress(i);
    if (!EXPO_VALID(ed)) break; // end of list
    if (ed->chn == cur_chn)
      continue;
    if (ed->flightModes & (1<<mixerCurrentFlightMode))
      continue;
    if (getSwitch(ed->swtch)) {
      int16_t v = anas2[ed->chn];
      if (EXPO_MODE_ENABLE(ed, v)) {
#if defined(BOLD_FONT)
        if (mode==e_perout_mode_normal) mixVal[i].activeExpo = true;
#endif
        cur_chn = ed->chn;

        //========== CURVE=================
        int8_t curveParam = ed->curveParam;
        if (curveParam) {
          if (ed->curveMode == MODE_CURVE)
            v = applyCurve(v, curveParam);
          else
            v = expo(v, GET_GVAR(curveParam, -100, 100, mixerCurrentFlightMode));
        }

        //========== WEIGHT ===============
        int16_t weight = GET_GVAR(ed->weight, MIN_EXPO_WEIGHT, 100, mixerCurrentFlightMode);
        weight = calc100to256(weight);
        v = ((int32_t)v * weight) >> 8;

        anas[cur_chn] = v;
      }
    }
  }
}

// #define PREVENT_ARITHMETIC_OVERFLOW
// because of optimizations the reserves before overruns occurs is only the half
// this defines enables some checks the greatly improves this situation
// It should nearly prevent all overruns (is still a chance for it, but quite low)
// negative side is code cost 96 bytes flash

// we do it now half way, only in applyLimits, which costs currently 50bytes
// according opinion poll this topic is currently not very important
// the change below improves already the situation
// the check inside mixer would slow down mix a little bit and costs additionally flash
// also the check inside mixer still is not bulletproof, there may be still situations a overflow could occur
// a bulletproof implementation would take about additional 100bytes flash
// therefore with go with this compromize, interested people could activate this define

// @@@2 open.20.fsguruh ;
// channel = channelnumber -1;
// value = outputvalue with 100 mulitplied usual range -102400 to 102400; output -1024 to 1024
// changed rescaling from *100 to *256 to optimize performance
// rescaled from -262144 to 262144
int16_t applyLimits(uint8_t channel, int32_t value)
{
  LimitData * lim = limitAddress(channel);

  int16_t ofs   = LIMIT_OFS_RESX(lim);
  int16_t lim_p = LIMIT_MAX_RESX(lim);
  int16_t lim_n = LIMIT_MIN_RESX(lim);

  ofs = limit<int16_t>(lim_n, ofs, lim_p);

  // because the rescaling optimization would reduce the calculation reserve we activate this for all builds
  // it increases the calculation reserve from factor 20,25x to 32x, which it slightly better as original
  // without it we would only have 16x which is slightly worse as original, we should not do this

  // thanks to gbirkus, he motivated this change, which greatly reduces overruns
  // unfortunately the constants and 32bit compares generates about 50 bytes codes; didn't find a way to get it down.
  value = limit(int32_t(-RESXl*256), value, int32_t(RESXl*256));  // saves 2 bytes compared to other solutions up to now

#if defined(PPM_LIMITS_SYMETRICAL)
  if (value) {
    int16_t tmp;
    if (lim->symetrical)
      tmp = (value > 0) ? (lim_p) : (-lim_n);
    else
      tmp = (value > 0) ? (lim_p - ofs) : (-lim_n + ofs);
    value = (int32_t) value * tmp;   //  div by 1024*256 -> output = -1024..1024
#else
  if (value) {
    int16_t tmp = (value > 0) ? (lim_p - ofs) : (-lim_n + ofs);
    value = (int32_t) value * tmp;   //  div by 1024*256 -> output = -1024..1024
#endif

#ifdef CORRECT_NEGATIVE_SHIFTS
    int8_t sign = (value<0?1:0);
    value -= sign;
    tmp = value>>16;   // that's quite tricky: the shiftright 16 operation is assmbled just with addressmove; just forget the two least significant bytes;
    tmp >>= 2;   // now one simple shift right for two bytes does the rest
    tmp += sign;
#else
    tmp = value>>16;   // that's quite tricky: the shiftright 16 operation is assmbled just with addressmove; just forget the two least significant bytes;
    tmp >>= 2;   // now one simple shift right for two bytes does the rest
#endif

    ofs += tmp;  // ofs can to added directly because already recalculated,
  }

  ofs = limit<int16_t>(lim_n, ofs, lim_p);

  if (lim->revert) ofs = -ofs; // finally do the reverse.

#if defined(OVERRIDE_CHANNEL_FUNCTION)
  if (safetyCh[channel] != OVERRIDE_CHANNEL_UNDEFINED) {
    // safety channel available for channel check
    ofs = calc100toRESX(safetyCh[channel]);
  }
#endif

  return ofs;
}

getvalue_t getValue(mixsrc_t i)
{
  if (i==MIXSRC_NONE) return 0;

  else if IS_IN_RANGE(i, MIXSRC_FIRST_STICK, MIXSRC_LAST_POT) return calibratedStick[i-MIXSRC_Rud];

  else if (i<MIXSRC_LAST_ROTARY_ENCODER+1) return getRotaryEncoder(i-MIXSRC_REa);

  else if (i==MIXSRC_MAX) return 1024;

  else if (i<MIXSRC_CYC3+1)
#if defined(HELI)
    return cyc_anas[i-MIXSRC_CYC1];
#else
    return 0;
#endif

  else if (i<MIXSRC_TrimAil+1) return calc1000toRESX((int16_t)8 * getTrimValue(mixerCurrentFlightMode, i-MIXSRC_TrimRud));
  else if (i==MIXSRC_3POS) return (getSwitch(SW_ID0-SW_BASE+1) ? -1024 : (getSwitch(SW_ID1-SW_BASE+1) ? 0 : 1024));
  // don't use switchState directly to give getSwitch possibility to hack values if needed for switch warning
  else if (i<MIXSRC_SW1) return getSwitch(SWSRC_THR+i-MIXSRC_THR) ? 1024 : -1024;
  else if (i<MIXSRC_LAST_LOGICAL_SWITCH+1) return getSwitch(SWSRC_FIRST_LOGICAL_SWITCH+i-MIXSRC_FIRST_LOGICAL_SWITCH) ? 1024 : -1024;
  else if (i<MIXSRC_LAST_TRAINER+1) {
    int16_t x = ppmInput[i-MIXSRC_FIRST_TRAINER];
    if (i<MIXSRC_FIRST_TRAINER+NUM_CAL_PPM) {
      x-= g_eeGeneral.trainer.calib[i-MIXSRC_FIRST_TRAINER];
    }
    return x*2;
  } else if (i<MIXSRC_LAST_CH+1) return ex_chans[i-MIXSRC_CH1];

#if defined(GVARS)
  else if (i<MIXSRC_LAST_GVAR+1) return GVAR_VALUE(i-MIXSRC_GVAR1, getGVarFlightPhase(mixerCurrentFlightMode, i-MIXSRC_GVAR1));
#endif

  else if (i==MIXSRC_FIRST_TELEM-1+TELEM_TX_VOLTAGE) return g_vbat10mV/10;
  else if (i<MIXSRC_FIRST_TELEM+TELEM_TIMER2) return timersStates[i-MIXSRC_FIRST_TELEM+1-TELEM_TIMER1].val;

#if defined(FRSKY)
  else if (i==MIXSRC_FIRST_TELEM-1+TELEM_RSSI_TX) return telemetryData.rssi[1].value;
  else if (i==MIXSRC_FIRST_TELEM-1+TELEM_RSSI_RX) return telemetryData.rssi[0].value;
  else if (i==MIXSRC_FIRST_TELEM-1+TELEM_A1) return telemetryData.analog[TELEM_ANA_A1].value;
  else if (i==MIXSRC_FIRST_TELEM-1+TELEM_A2) return telemetryData.analog[TELEM_ANA_A2].value;
  else if (i==MIXSRC_FIRST_TELEM-1+TELEM_ALT) return TELEMETRY_RELATIVE_BARO_ALT_BP;
  else if (i==MIXSRC_FIRST_TELEM-1+TELEM_RPM) return telemetryData.value.rpm;
  else if (i==MIXSRC_FIRST_TELEM-1+TELEM_FUEL) return telemetryData.value.fuelLevel;
  else if (i==MIXSRC_FIRST_TELEM-1+TELEM_T1) return telemetryData.value.temperature1;
  else if (i==MIXSRC_FIRST_TELEM-1+TELEM_T2) return telemetryData.value.temperature2;
  else if (i==MIXSRC_FIRST_TELEM-1+TELEM_SPEED) return TELEMETRY_GPS_SPEED_BP;
  else if (i==MIXSRC_FIRST_TELEM-1+TELEM_DIST) return telemetryData.value.gpsDistance;
  else if (i==MIXSRC_FIRST_TELEM-1+TELEM_GPSALT) return telemetryData.value.gpsAltitude;
  else if (i==MIXSRC_FIRST_TELEM-1+TELEM_CELL) return (int16_t)TELEMETRY_MIN_CELL_VOLTAGE;
  else if (i==MIXSRC_FIRST_TELEM-1+TELEM_CELLS_SUM) return (int16_t)telemetryData.value.cellsSum;
  else if (i==MIXSRC_FIRST_TELEM-1+TELEM_VFAS) return (int16_t)telemetryData.value.vfas;
  else if (i==MIXSRC_FIRST_TELEM-1+TELEM_CURRENT) return (int16_t)telemetryData.value.current;
  else if (i==MIXSRC_FIRST_TELEM-1+TELEM_CONSUMPTION) return telemetryData.value.currentConsumption;
  else if (i==MIXSRC_FIRST_TELEM-1+TELEM_POWER) return telemetryData.value.power;
  else if (i==MIXSRC_FIRST_TELEM-1+TELEM_ACCx) return telemetryData.value.accelX;
  else if (i==MIXSRC_FIRST_TELEM-1+TELEM_ACCy) return telemetryData.value.accelY;
  else if (i==MIXSRC_FIRST_TELEM-1+TELEM_ACCz) return telemetryData.value.accelZ;
  else if (i==MIXSRC_FIRST_TELEM-1+TELEM_HDG) return telemetryData.value.gpsCourse_bp;
  else if (i==MIXSRC_FIRST_TELEM-1+TELEM_VSPEED) return telemetryData.value.varioSpeed;
  else if (i==MIXSRC_FIRST_TELEM-1+TELEM_ASPEED) return telemetryData.value.airSpeed;
  else if (i==MIXSRC_FIRST_TELEM-1+TELEM_DTE) return telemetryData.value.dTE;
  else if (i<=MIXSRC_FIRST_TELEM-1+TELEM_MIN_A1) return telemetryData.analog[TELEM_ANA_A1].min;
  else if (i==MIXSRC_FIRST_TELEM-1+TELEM_MIN_A2) return telemetryData.analog[TELEM_ANA_A2].min;
  else if (i<=MIXSRC_FIRST_TELEM-1+TELEM_CSW_MAX) return *(((int16_t*)(&telemetryData.value.minAltitude))+i-(MIXSRC_FIRST_TELEM-1+TELEM_MIN_ALT));
#endif
  else return 0;
}

void evalInputs(uint8_t mode)
{
  BeepANACenter anaCenter = 0;

#if defined(HELI)
  uint16_t d = 0;
  if (g_model.swashR.value) {
    uint32_t v = (int32_t(calibratedStick[ELE_STICK])*calibratedStick[ELE_STICK] + int32_t(calibratedStick[AIL_STICK])*calibratedStick[AIL_STICK]);
    uint32_t q = calc100toRESX(g_model.swashR.value);
    q *= q;
    if (v > q) {
      d = isqrt32(v);
    }
  }
#endif

  for (uint8_t i=0; i<NUM_STICKS+NUM_POTS+NUM_ROTARY_ENCODERS; i++) {

    // normalization [0..2048] -> [-1024..1024]
    uint8_t ch = (i < NUM_STICKS ? CONVERT_MODE(i) : i);

    int16_t v = ((i < NUM_STICKS+NUM_POTS) ? anaIn(i) : getRotaryEncoder(i-(NUM_STICKS+NUM_POTS)));

    if (i < NUM_STICKS+NUM_POTS) {
      if (IS_POT_MULTIPOS(i)) {
        v -= RESX;
      } else {
        CalibData * calib = &g_eeGeneral.calib[i];
        v -= calib->mid;
        v = v * (int32_t)RESX / (max((int16_t)100, (v>0 ? calib->spanPos : calib->spanNeg)));
      }
    }

    v = limit<int16_t>(-RESX, v, RESX);

    BeepANACenter mask = (BeepANACenter)1 << ch;

    if (i < NUM_STICKS+NUM_POTS) {

      calibratedStick[ch] = v; // for show in expo

      // filtering for center beep
      uint8_t tmp = (uint16_t)abs(v) / 16;
      if (tmp <= 1) anaCenter |= (tmp==0 ? mask : (bpanaCenter & mask));
    } else {
      // rotary encoders
      if (v == 0) anaCenter |= mask;
    }

    if (ch < NUM_STICKS) { //only do this for sticks

      if (mode <= e_perout_mode_inactive_flight_mode && isFunctionActive(FUNCTION_TRAINER+ch) && IS_TRAINER_INPUT_VALID()) {
        // trainer mode
        TrainerMix* td = &g_eeGeneral.trainer.mix[ch];
        if (td->mode) {
          uint8_t chStud = td->srcChn;
          int32_t vStud  = (ppmInput[chStud]- g_eeGeneral.trainer.calib[chStud]);
          vStud *= td->studWeight;
          vStud /= 50;
          switch (td->mode) {
          case 1:
            // add-mode
            v = limit<int16_t>(-RESX, v+vStud, RESX);
            break;
          case 2:
            // subst-mode
            v = vStud;
            break;
          }
        }
      }

#if defined(HELI)
      if (d && (ch==ELE_STICK || ch==AIL_STICK)) {
        v = (int32_t(v) * calc100toRESX(g_model.swashR.value)) / int32_t(d);
      }
#endif
      rawAnas[ch] = v;
      anas[ch] = v; // set values for mixer
    }
  }

  /* EXPOs */
  applyExpos(anas, mode);

  /* TRIMs */
  evalTrims(); // when no virtual inputs, the trims need the anas array calculated above (when throttle trim enabled)

  if (mode == e_perout_mode_normal) {
    anaCenter &= g_model.beepANACenter;
    if (((bpanaCenter ^ anaCenter) & anaCenter)) AUDIO_POT_MIDDLE();
    bpanaCenter = anaCenter;
  }
}

uint8_t mixerCurrentFlightMode;

void evalFlightModeMixes(uint8_t mode, uint8_t tick10ms)
{
  evalInputs(mode);

#if defined(HELI)
  int16_t heliEleValue = anas[ELE_STICK];
  int16_t heliAilValue = anas[AIL_STICK];
  if (g_model.swashR.value) {
    uint32_t v = ((int32_t)heliEleValue*heliEleValue + (int32_t)heliAilValue*heliAilValue);
    uint32_t q = calc100toRESX(g_model.swashR.value);
    q *= q;
    if (v>q) {
      uint16_t d = isqrt32(v);
      int16_t tmp = calc100toRESX(g_model.swashR.value);
      heliEleValue = (int32_t) heliEleValue*tmp/d;
      heliAilValue = (int32_t) heliAilValue*tmp/d;
    }
  }

#define REZ_SWASH_X(x)  ((x) - (x)/8 - (x)/128 - (x)/512)   //  1024*sin(60) ~= 886
#define REZ_SWASH_Y(x)  ((x))   //  1024 => 1024

  if (g_model.swashR.type) {
    getvalue_t vp = heliEleValue + trims[ELE_STICK];
    getvalue_t vr = heliAilValue + trims[AIL_STICK];
    getvalue_t vc = 0;
    if (g_model.swashR.collectiveSource)
      vc = getValue(g_model.swashR.collectiveSource);

    if (g_model.swashR.invertELE) vp = -vp;
    if (g_model.swashR.invertAIL) vr = -vr;
    if (g_model.swashR.invertCOL) vc = -vc;

    switch (g_model.swashR.type) {
    case SWASH_TYPE_120:
      vp = REZ_SWASH_Y(vp);
      vr = REZ_SWASH_X(vr);
      cyc_anas[0] = vc - vp;
      cyc_anas[1] = vc + vp/2 + vr;
      cyc_anas[2] = vc + vp/2 - vr;
      break;
    case SWASH_TYPE_120X:
      vp = REZ_SWASH_X(vp);
      vr = REZ_SWASH_Y(vr);
      cyc_anas[0] = vc - vr;
      cyc_anas[1] = vc + vr/2 + vp;
      cyc_anas[2] = vc + vr/2 - vp;
      break;
    case SWASH_TYPE_140:
      vp = REZ_SWASH_Y(vp);
      vr = REZ_SWASH_Y(vr);
      cyc_anas[0] = vc - vp;
      cyc_anas[1] = vc + vp + vr;
      cyc_anas[2] = vc + vp - vr;
      break;
    case SWASH_TYPE_90:
      vp = REZ_SWASH_Y(vp);
      vr = REZ_SWASH_Y(vr);
      cyc_anas[0] = vc - vp;
      cyc_anas[1] = vc + vr;
      cyc_anas[2] = vc - vr;
      break;
    default:
      break;
    }
  }
#endif

  memclear(chans, sizeof(chans));        // All outputs to 0

  //========== MIXER LOOP ===================
  uint8_t lv_mixWarning = 0;
  uint8_t pass = 0;

  bitfield_channels_t dirtyChannels = (bitfield_channels_t)-1; // all dirty when mixer starts

  do {

    bitfield_channels_t passDirtyChannels = 0;

    for (uint8_t i=0; i<MAX_MIXERS; i++) {

#if defined(BOLD_FONT)
      if (mode==e_perout_mode_normal && pass==0) mixVal[i].activeMix = false;
#endif

      MixData *md = mixAddress(i);

      if (md->srcRaw == 0) break;

      mixsrc_t stickIndex = md->srcRaw - MIXSRC_Rud;

      if (!(dirtyChannels & ((bitfield_channels_t)1 << md->destCh))) continue;


      //========== PHASE && SWITCH ==========
      uint8_t mixCondition = (md->flightModes != 0 || md->swtch);
      delayval_t mixEnabled = (!(md->flightModes & (1 << mixerCurrentFlightMode)) && getSwitch(md->swtch)) ? 1 : 0;
#define MIXER_LINE_DISABLE()  (mixCondition = true, mixEnabled = 0)
      if (mixEnabled && md->srcRaw >= MIXSRC_FIRST_TRAINER && md->srcRaw <= MIXSRC_LAST_TRAINER && !IS_TRAINER_INPUT_VALID()) {
        MIXER_LINE_DISABLE();
      }

      //========== VALUE ====================
      getvalue_t v = 0;
      if (mode > e_perout_mode_inactive_flight_mode) {
        if (!mixEnabled || stickIndex >= NUM_STICKS || (stickIndex == THR_STICK && g_model.thrTrim)) {
          continue;
        } else {
          if (!(mode & e_perout_mode_nosticks)) v = anas[stickIndex];
        }
      } else {
        if (stickIndex < NUM_STICKS) {
          v = md->noExpo ? rawAnas[stickIndex] : anas[stickIndex];
        } else {
          mixsrc_t srcRaw = MIXSRC_Rud + stickIndex;
          v = getValue(srcRaw);
          srcRaw -= MIXSRC_CH1;
          if (srcRaw<=MIXSRC_LAST_CH-MIXSRC_CH1 && md->destCh != srcRaw) {
            if (dirtyChannels & ((bitfield_channels_t)1 << srcRaw) & (passDirtyChannels|~(((bitfield_channels_t) 1 << md->destCh)-1)))
              passDirtyChannels |= (bitfield_channels_t) 1 << md->destCh;
            if (srcRaw < md->destCh || pass > 0)
              v = chans[srcRaw]>>8;
          }
        }
        if (!mixCondition) {
          mixEnabled = v>>10;
        }
      }

        //========== GAZ SECURITY ============
        if (md->srcRaw == gazSecurity.gazSource)
        {
          if (getSwitch(g_model.thrSwitch ? g_model.thrSwitch+3 : SWSRC_NONE))
          {
            if (v <= (-RESX+10))
              gazSecurity.enableGaz = true;
          }
          else
          {
            gazSecurity.enableGaz = false;
          }
          if (!gazSecurity.enableGaz)
            v = - RESX; // Gaz to min.
        }


      //========== DELAYS ===================
        if (mode == e_perout_mode_normal && (md->delayDown || md->delayUp)) // there are delay values
          {
            int16_t d_diff = v - mixVal[i].hold;
            if (!mixVal[i].delay && d_diff) // There is no delay running and value change
              {
                if (systemBolls.s_mixer_first_run_done)
                {
                  mixVal[i].delay = (d_diff > 0 ? md->delayUp : md->delayDown) * (100/DELAY_STEP); // init delay
                }
              mixVal[i].hold = v;     // store actual value of v as reference for next run
              }
              else
              {
               if (abs(d_diff) > 10) mixVal[i].delay = max<int16_t>(0, (int16_t)mixVal[i].delay - tick10ms); // decrement delay if diff is more than 10
                v = mixVal[i].hold;     // keep v to stored value until end of delay
              }
          }

      //========== SLOW DOWN ================
      // lower weight causes slower movement
      if (mode <= e_perout_mode_inactive_flight_mode && (md->speedUp || md->speedDown)) { // there are slow-down values
        int32_t tact = mixVal[i].act;
        int16_t diff = v - (tact>>8);  // we recale to a mult 256 higher value for calculation
        if (diff) {
          // open.20.fsguruh: speed is defined in % movement per second; In menu we specify the full movement (-100% to 100%) = 200% in total
          // the unit of the stored value is the value from md->speedUp or md->speedDown divide SLOW_STEP seconds; e.g. value 4 means 4/SLOW_STEP = 2 seconds for CPU64
          // because we get a tick each 10msec, we need 100 ticks for one second
          // the value in md->speedXXX gives the time it should take to do a full movement from -100 to 100 therefore 200%. This equals 2048 in recalculated internal range
          if (tick10ms || !systemBolls.s_mixer_first_run_done) {
            // only if already time is passed add or substract a value according the speed configured
            int32_t rate = (int32_t)tick10ms<<(8+11);  // = 256*2048*tick10ms
            // rate equals a full range for one second; if less time is passed rate is accordingly smaller
            // if one second passed, rate would be 2048(full motion)*256(recalculated weight)*100(100 ticks needed for one second)
            int32_t currentValue = (int32_t)v<<8;
              if (systemBolls.s_mixer_first_run_done)
                {
                  if ((diff > 0) && md->speedUp)
                    {
                      // if a speed upwards is defined recalculate the new value according configured speed; the higher the speed the smaller the add value is
                      int32_t newValue = tact+rate/((int16_t)(100/SLOW_STEP)*md->speedUp);
                      if (newValue<currentValue)
                        currentValue = newValue; // Endposition; prevent toggling around the destination
                    }
                  else   // if is <0 because ==0 is not possible
                    {
                      if (md->speedDown)
                        {
                          // see explanation in speedUp
                          int32_t newValue = tact-rate/((int16_t)(100/SLOW_STEP)*md->speedDown);
                          if (newValue>currentValue)
                            currentValue = newValue; // Endposition; prevent toggling around the destination
                        }
                    }
                }
              mixVal[i].act = tact = currentValue;
            // open.20.fsguruh: this implementation would save about 50 bytes code
          } // endif tick10ms ; in case no time passed assign the old value, not the current value from source
          v = tact>>8;
        }
      }

      //========== Active Mix ===============
      uint8_t apply_offset_and_curve = true;
      if (!mixEnabled) {
        if ((md->delayDown || md->delayUp) && md->mltpx!=MLTPX_REP) {
          if (mixCondition) {
            v = (md->mltpx == MLTPX_ADD ? 0 : RESX);
            apply_offset_and_curve = false;
          }
        } else if (mixCondition) {
          continue;
        }
      }
      if (mode==e_perout_mode_normal && (!mixCondition || mixEnabled || mixVal[i].delay)) {
        if (md->mixWarn) lv_mixWarning |= 1 << (md->mixWarn - 1);
#if defined(BOLD_FONT)
        mixVal[i].activeMix = true;
#endif
      }

      //========== OFFSET BEFORE ============
#if defined(OFFSET_ON_INPUT)
      if (apply_offset_and_curve) {
        int16_t offset = GET_GVAR(MD_OFFSET(md), GV_RANGELARGE_NEG, GV_RANGELARGE, mixerCurrentFlightMode);
        if (offset) v += calc100toRESX_16Bits(offset);
      }
#endif

      //========== TRIMS ====================
      int16_t trim = 0;
      if (apply_offset_and_curve &&!(mode & e_perout_mode_notrims)) {
          int8_t mix_trim = md->carryTrim;
          if (mix_trim < TRIM_ON)
            mix_trim = -mix_trim - 1;
          else if (mix_trim == TRIM_ON && stickIndex < NUM_STICKS)
            mix_trim = stickIndex;
          else
            mix_trim = -1;
          if (mix_trim >= 0) {
            trim = trims[mix_trim];
        }
      }

      //========== CURVES ==================
      if (apply_offset_and_curve && md->curveMode != MODE_DIFFERENTIAL) {
        v += trim;
        if (md->curveMode == MODE_CURVE && md->curveParam) {
          v = applyCurve(v, md->curveParam);
        }
      }

      //========== WEIGHT ===================
      int16_t weight = GET_GVAR(MD_WEIGHT(md), GV_RANGELARGE_NEG, GV_RANGELARGE, mixerCurrentFlightMode);
      weight = calc100to256_16Bits(weight);
      int32_t dv = (int32_t) v * weight;
      int32_t dtrim = (int32_t) trim * weight;

      //========== DIFFERENTIAL =============
      if (md->curveMode == MODE_DIFFERENTIAL) {
        // stick and trim are computed separatly
        // @@@2 also recalculate curveParam to a 256 basis which ease the calculation later a lot
        int16_t curveParam = calc100to256(GET_GVAR(md->curveParam, -100, 100, mixerCurrentFlightMode));
        if (curveParam > 0 && dv < 0) {
          dv = (dv * (256 - curveParam)) >> 8;
        } else if (curveParam < 0 && dv > 0) {
          dv = (dv * (256 + curveParam)) >> 8;
        }
        if (curveParam > 0 && dtrim < 0) {
          dtrim = (dtrim * (256 - curveParam)) >> 8;
        } else if (curveParam < 0 && dtrim > 0) {
          dtrim = (dtrim * (256 + curveParam)) >> 8;
        }
        dv += dtrim;
      }

      //========== OFFSET AFTER =============
#if !defined(OFFSET_ON_INPUT)
      if (apply_offset_and_curve) {
        int16_t offset = GET_GVAR(MD_OFFSET(md), GV_RANGELARGE_NEG, GV_RANGELARGE, mixerCurrentFlightMode);
        if (offset) dv += int32_t(calc100toRESX_16Bits(offset)) << 8;
      }

#endif

      //Stick value to mixer
      //    stick => delay => slow_down => mixer source

      //Mixer output with offset before
      //    Curve(source + offset + trim) * weight
      //    Diff((source + offset) * weight) + Diff(trim * weight)

      //Mixer output with offset after
      //    Curve(source + trim) * weight + offset
      //    Diff(source * weight) + Diff(trim * weight) + offset

      int32_t *ptr = &chans[md->destCh]; // Save calculating address several times

      switch (md->mltpx) {
      case MLTPX_REP:
        *ptr = dv;
#if defined(BOLD_FONT)
        if (mode==e_perout_mode_normal) {
          for (uint8_t m=i-1; m<MAX_MIXERS && mixAddress(m)->destCh==md->destCh; m--)
            mixVal[m].activeMix = false;
        }
#endif
        break;
      case MLTPX_MUL:
        // @@@2 we have to remove the weight factor of 256 in case of 100%; now we use the new base of 256
        dv >>= 8;
        dv *= *ptr;
        dv >>= RESX_SHIFT;   // same as dv /= RESXl;
        *ptr = dv;
        break;
      default: // MLTPX_ADD
        *ptr += dv; //Mixer output add up to the line (dv + (dv>0 ? 100/2 : -100/2))/(100);
        break;
      } //endswitch md->mltpx

#ifdef PREVENT_ARITHMETIC_OVERFLOW
      /*
            // a lot of assumptions must be true, for this kind of check; not really worth for only 4 bytes flash savings
            // this solution would save again 4 bytes flash
            int8_t testVar=(*ptr<<1)>>24;
            if ( (testVar!=-1) && (testVar!=0 ) ) {
              // this devices by 64 which should give a good balance between still over 100% but lower then 32x100%; should be OK
              *ptr >>= 6;  // this is quite tricky, reduces the value a lot but should be still over 100% and reduces flash need
            } */

      PACK( union u_int16int32_t {
        struct {
          int16_t lo;
          int16_t hi;
        } words_t;
        int32_t dword;
      });

      u_int16int32_t tmp;
      tmp.dword=*ptr;

      if (tmp.dword<0) {
        if ((tmp.words_t.hi&0xFF80)!=0xFF80) tmp.words_t.hi=0xFF86; // set to min nearly
      } else {
        if ((tmp.words_t.hi|0x007F)!=0x007F) tmp.words_t.hi=0x0079; // set to max nearly
      }
      *ptr = tmp.dword;
      // this implementation saves 18bytes flash

      /*      dv=*ptr>>8;
            if (dv>(32767-RESXl)) {
              *ptr=(32767-RESXl)<<8;
            } else if (dv<(-32767+RESXl)) {
              *ptr=(-32767+RESXl)<<8;
            }*/
      // *ptr=limit( int32_t(int32_t(-1)<<23), *ptr, int32_t(int32_t(1)<<23));  // limit code cost 72 bytes
      // *ptr=limit( int32_t((-32767+RESXl)<<8), *ptr, int32_t((32767-RESXl)<<8));  // limit code cost 80 bytes
#endif

    } //endfor mixers

    tick10ms = 0;
    dirtyChannels &= passDirtyChannels;

  } while (++pass < 5 && dirtyChannels);

  mixWarning = lv_mixWarning;
}

#define MAX_ACT 0xffff
uint8_t lastFlightMode = 255; // TODO reinit everything here when the model changes, no???
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
