Ingwie/OpenAVRc_Dev/OpenAVRc/protocol/E129_cyrf6936.c

/*
 **************************************************************************
 *                                                                        *
 *                 ____                ___ _   _____                      *
 *                / __ \___  ___ ___  / _ | | / / _ \____                 *
 *               / /_/ / _ \/ -_) _ \/ __ | |/ / , _/ __/                 *
 *               \____/ .__/\__/_//_/_/ |_|___/_/|_|\__/                  *
 *                   /_/                                                  *
 *                                                                        *
 *              This file is part of the OpenAVRc project.                *
 *                                                                        *
 *                         Based on code(s) named :                       *
 *             OpenTx - https://github.com/opentx/opentx                  *
 *             Deviation - https://www.deviationtx.com/                   *
 *             Multiprotocol TX Module -                                  *
 *   https://github.com/pascallanger/DIY-Multiprotocol-TX-Module          *
 *                                                                        *
 *                Only AVR code here for visibility ;-)                   *
 *                                                                        *
 *   OpenAVRc is free software: you can redistribute it and/or modify     *
 *   it under the terms of the GNU General Public License as published by *
 *   the Free Software Foundation, either version 2 of the License, or    *
 *   (at your option) any later version.                                  *
 *                                                                        *
 *   OpenAVRc is distributed in the hope that it will be useful,          *
 *   but WITHOUT ANY WARRANTY; without even the implied warranty of       *
 *   MERCHANTABILITY or FITNESS FOR A PARTICULAR PURPOSE.  See the        *
 *   GNU General Public License for more details.                         *
 *                                                                        *
 *       License GPLv2: http://www.gnu.org/licenses/gpl-2.0.html          *
 *                                                                        *
 **************************************************************************
 */

/*
 * Models: Eachine E129 / E130, Hobbyking Firefox C129 and Twister Ninja 250.
 *
 *
 * Channel Order :
 * Ch1 A
 * Ch2 E
 * Ch3 T
 * Ch4 R
 * Ch5 Trim A
 * Ch6 Trim E
 * Ch7 Trim R
 * Logical Switch L3 Take Off / Land
 * Logical Switch L4 Emergency Stop
 *
 * Trims can be done to some extent on the AETR channels directly
 * but if you push them too far you won't be able to arm like explained below.
 * In this case use the associated trim TrimA/E/R instead.
 *
 * Take off with a none spring throttle is easier by putting both sticks down outwards
 * (like on the original radio) in Mode 1/2, not sure about other modes.
 *
 * Calibration is the same as the original radio with both sticks down and to the left in Mode 1/2,
 * not sure about other modes.
 *
 */
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
